CountDeMonet/ArduinoProtonPack/bargraph_rear.jpg

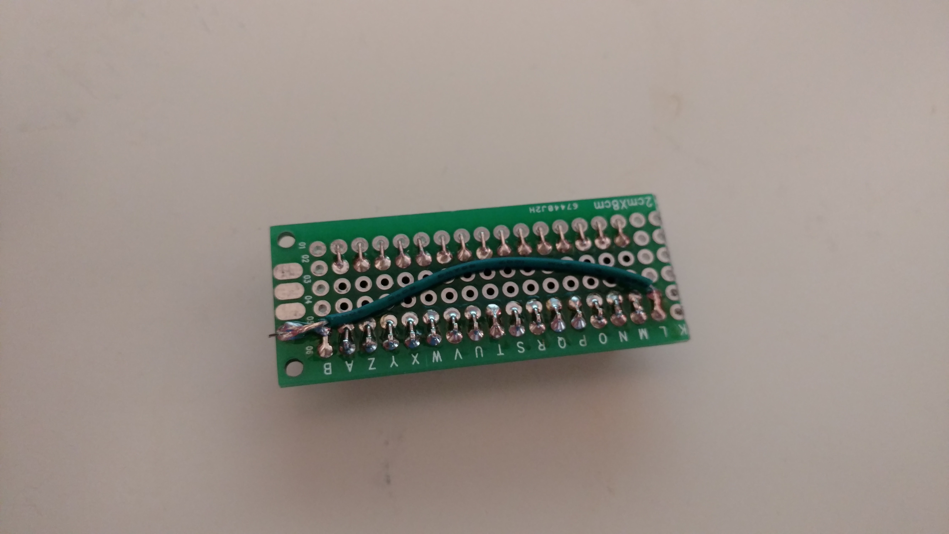
bargraph_rear.jpg
