CountDeMonet/ArduinoProtonPack/Model/83_Percent_Pack_Lefty/ion_3.stl

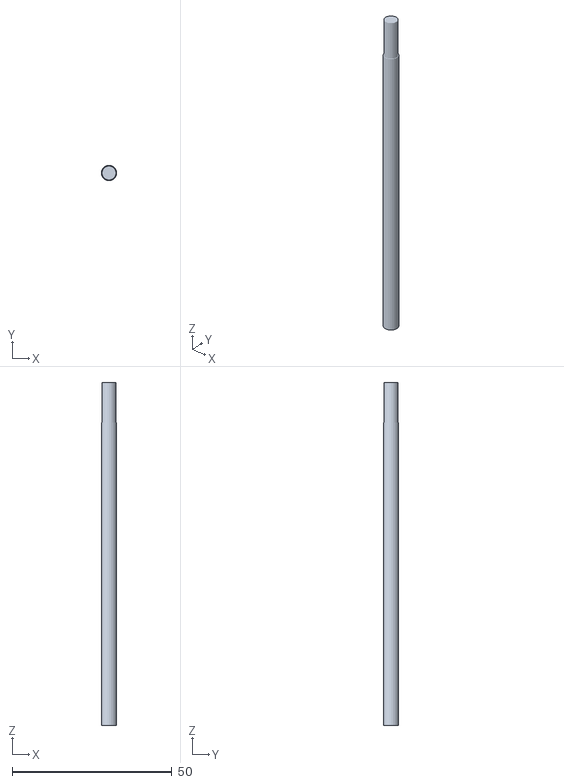
[picture p24: CAD file, 2017-09-11]
Model/83_Percent_Pack_Lefty/ion_3.stl
4.78 x 4.78 x 107.3
