CountDeMonet/ArduinoProtonPack/Model/83_Percent_Proton_Wand/front_handle_end_piece.stl

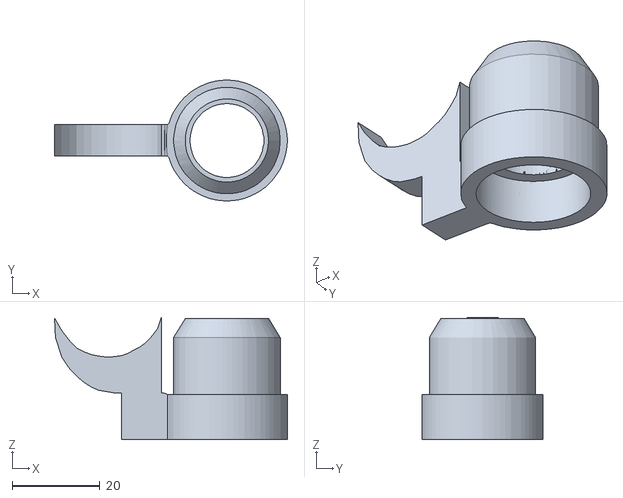
[picture p25: CAD file, 2017-10-17]
Model/83_Percent_Proton_Wand/front_handle_end_piece.stl
53.1 x 27.5 x 27.9
