CountDeMonet/ArduinoProtonPack/Model/SpiritHalloweenProtonPackMods/gunbracket_base.stl

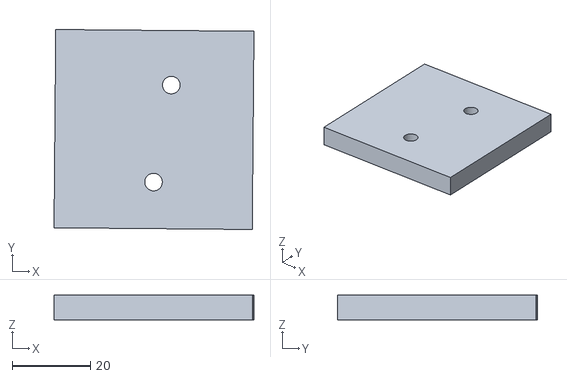
[picture p26: CAD file, 2017-10-16]
Model/SpiritHalloweenProtonPackMods/gunbracket_base.stl
51.2 x 51.2 x 6.35
