CountDeMonet/ArduinoProtonPack/Model/83_Percent_Pack/syncgen_5.stl

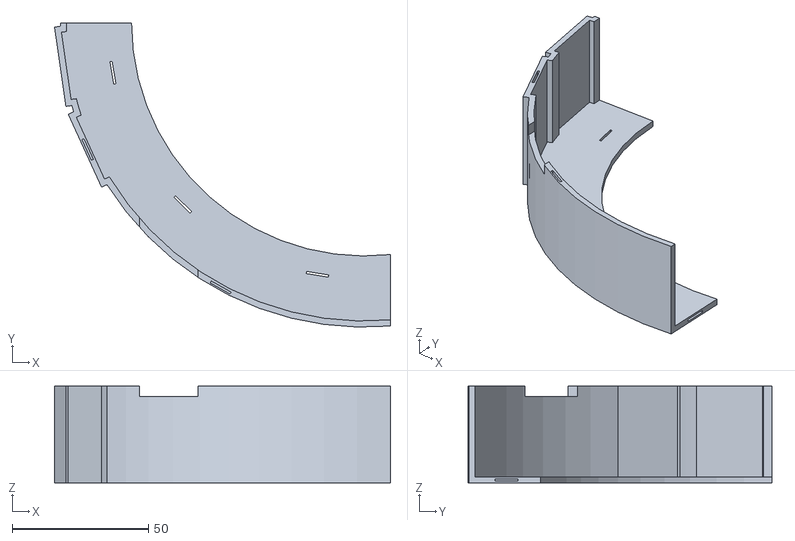
[picture p27: CAD file, 2017-10-23]
Model/83_Percent_Pack/syncgen_5.stl
123.1 x 111.4 x 35.5
