CountDeMonet/ArduinoProtonPack/Model/83_Percent_Proton_Wand/gunbox_back_panel_knob.stl

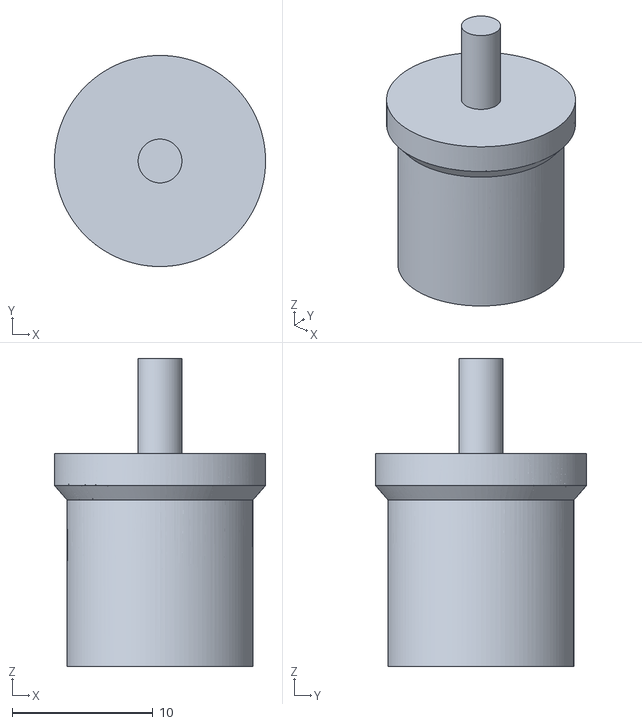
[picture p28: CAD file, 2017-10-08]
Model/83_Percent_Proton_Wand/gunbox_back_panel_knob.stl
15.0 x 15.0 x 21.9
