CountDeMonet/ArduinoProtonPack/Model/SpiritHalloweenProtonPackMods/powercell_neopixel_mount.stl

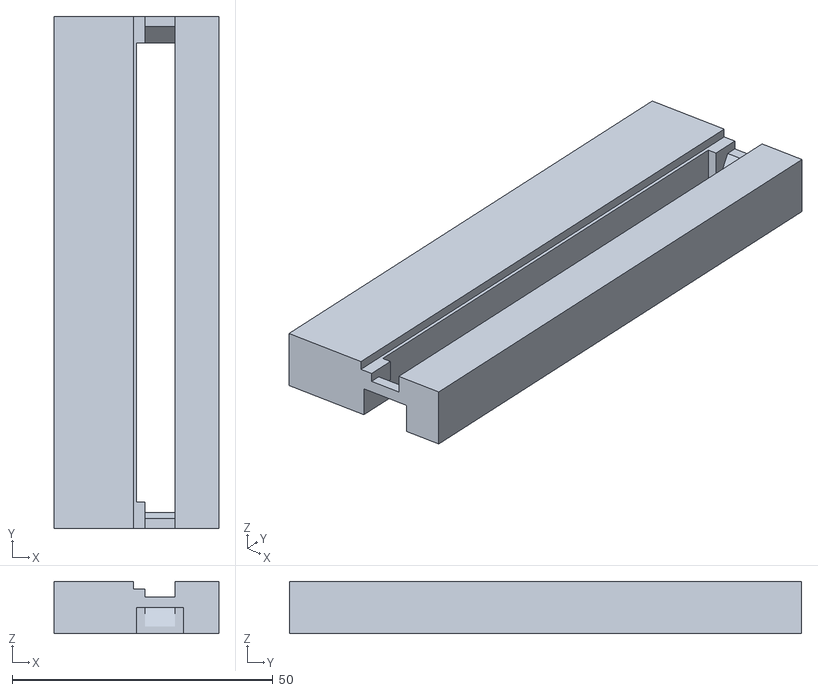
[picture p29: CAD file, 2017-10-15]
Model/SpiritHalloweenProtonPackMods/powercell_neopixel_mount.stl
31.6 x 98.2 x 10.00
