CountDeMonet/ArduinoProtonPack/Model/83_Percent_Pack/base_1.stl

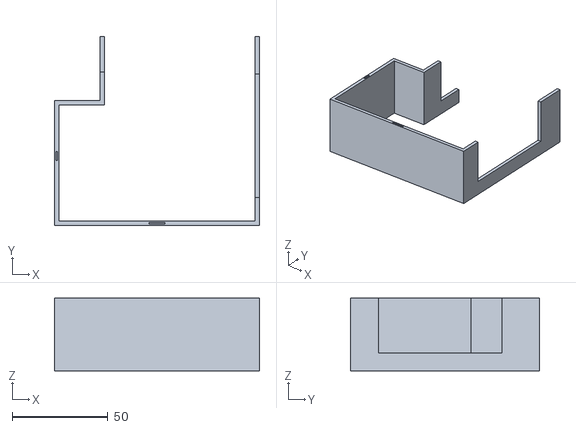
[picture p30: CAD file, 2017-10-23]
Model/83_Percent_Pack/base_1.stl
107.1 x 98.7 x 38.1
