CountDeMonet/ArduinoProtonPack/Model/83_Percent_Proton_Wand/front_green_tube_barbs.stl

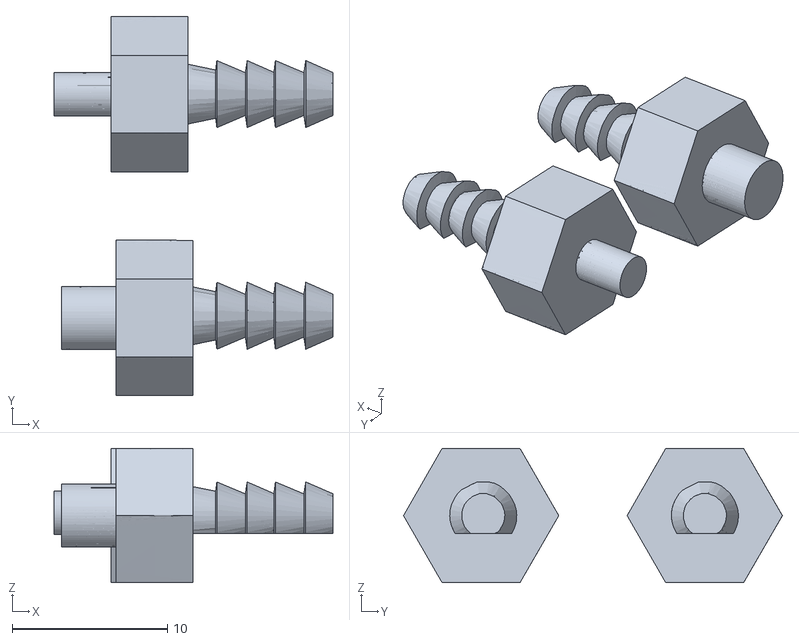
[picture p31: CAD file, 2017-10-07]
Model/83_Percent_Proton_Wand/front_green_tube_barbs.stl
17.9 x 24.4 x 8.66
