CountDeMonet/ArduinoProtonPack/Model/SpiritHalloweenProtonPackMods/cyclotron_individual_neopixel.stl

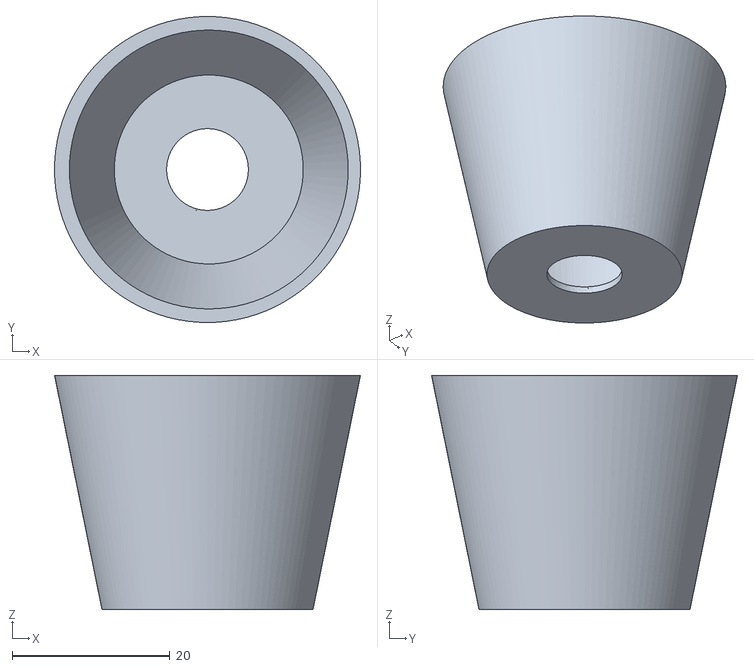
[picture p32: CAD file, 2017-10-14]
Model/SpiritHalloweenProtonPackMods/cyclotron_individual_neopixel.stl
38.8 x 38.8 x 29.7
