CountDeMonet/ArduinoProtonPack/Model/83_Percent_Pack/plating_3.stl

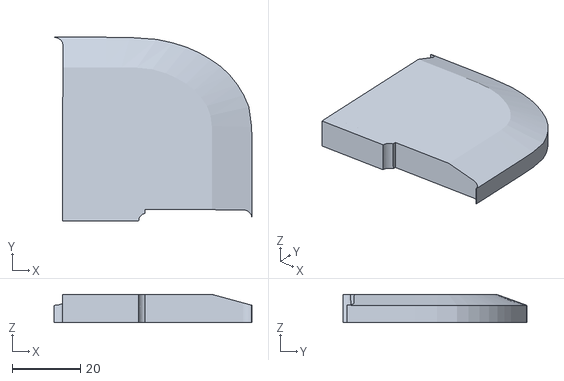
[picture p33: CAD file, 2017-10-23]
Model/83_Percent_Pack/plating_3.stl
58.1 x 53.9 x 8.30
