CountDeMonet/ArduinoProtonPack/Model/83_Percent_Proton_Wand/front_handle_hose_mount.stl

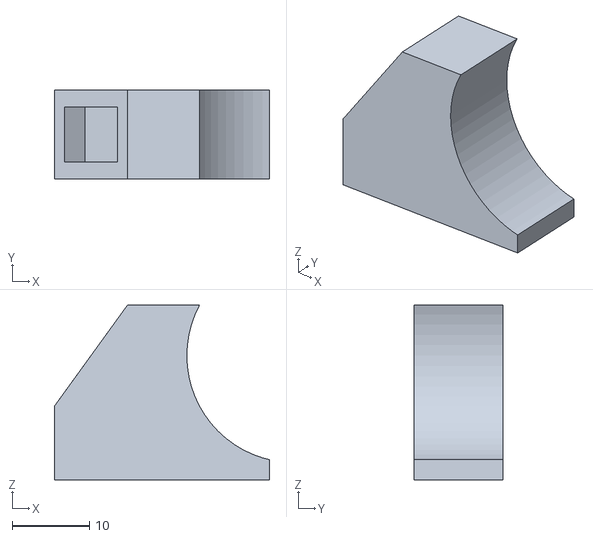
[picture p34: CAD file, 2017-09-26]
Model/83_Percent_Proton_Wand/front_handle_hose_mount.stl
27.8 x 11.4 x 22.6
