CountDeMonet/ArduinoProtonPack/Model/83_Percent_Pack/gunmount_3.stl

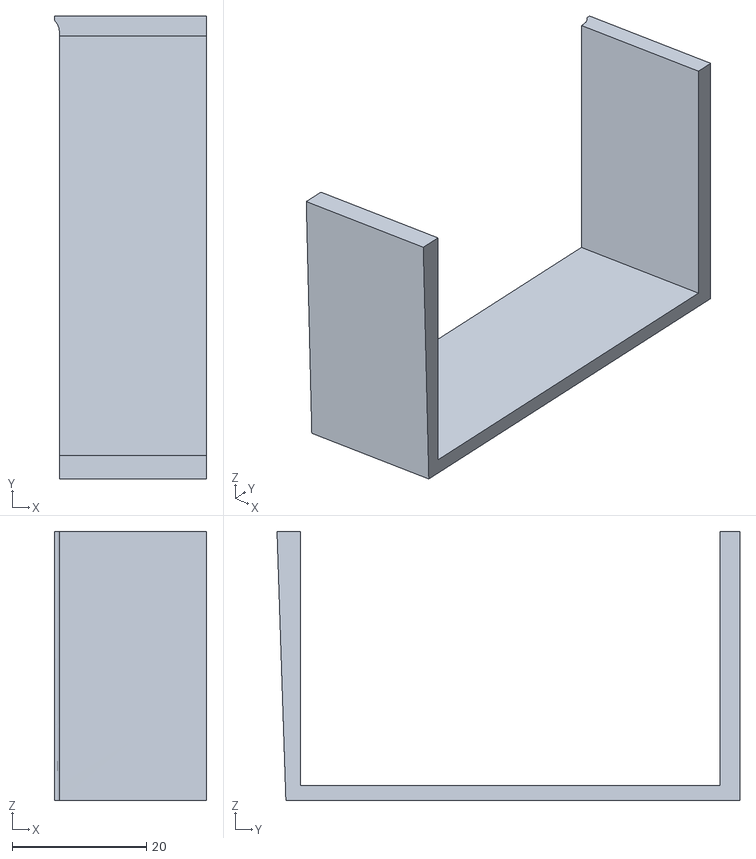
[picture p35: CAD file, 2017-10-23]
Model/83_Percent_Pack/gunmount_3.stl
22.7 x 69.0 x 40.1
