CountDeMonet/ArduinoProtonPack/Model/83_Percent_Proton_Wand/front_handle_finger_guard.stl

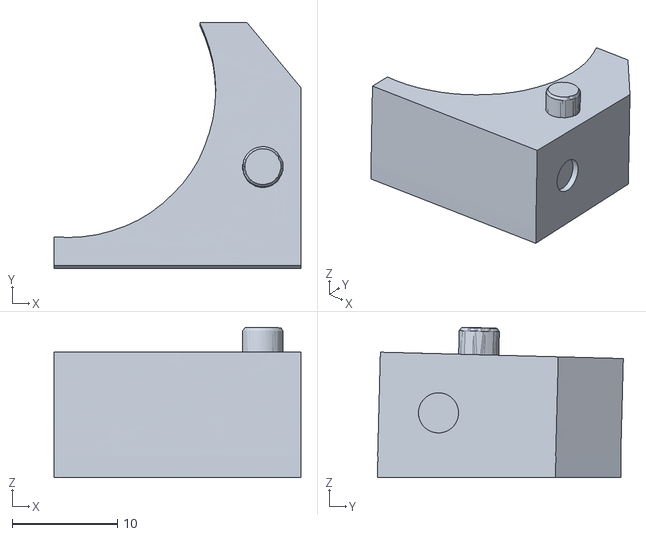
[picture p36: CAD file, 2017-09-26]
Model/83_Percent_Proton_Wand/front_handle_finger_guard.stl
23.5 x 23.4 x 14.3
