CountDeMonet/ArduinoProtonPack/Model/83_Percent_Pack/ion_1.stl

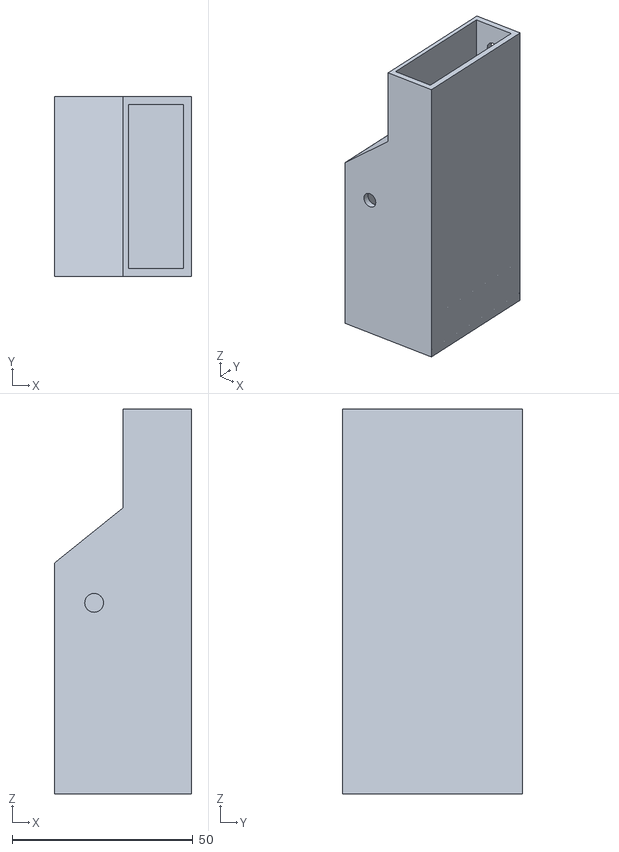
[picture p37: CAD file, 2017-10-23]
Model/83_Percent_Pack/ion_1.stl
38.0 x 49.8 x 106.6
