CountDeMonet/ArduinoProtonPack/Model/83_Percent_Proton_Wand/front_handle_wing.stl

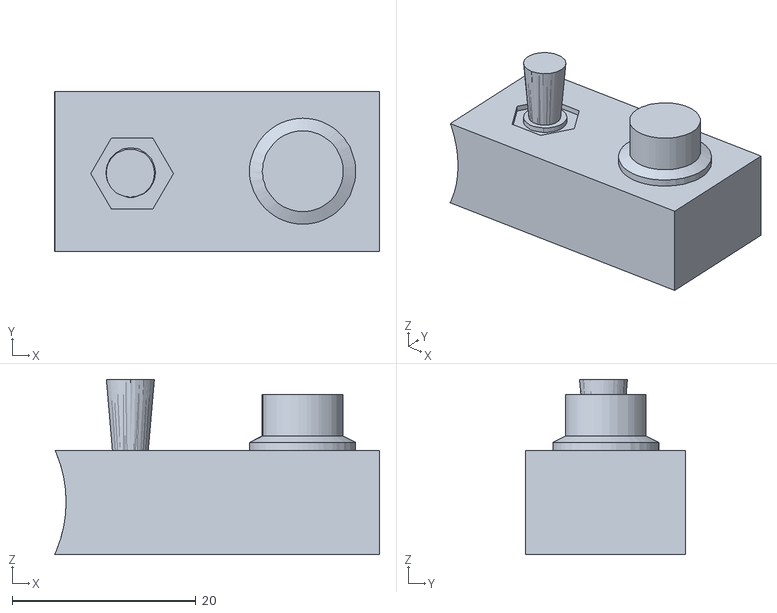
[picture p38: CAD file, 2017-09-26]
Model/83_Percent_Proton_Wand/front_handle_wing.stl
35.3 x 17.4 x 19.0
