CountDeMonet/ArduinoProtonPack/Model/83_Percent_Pack/booster_2.stl

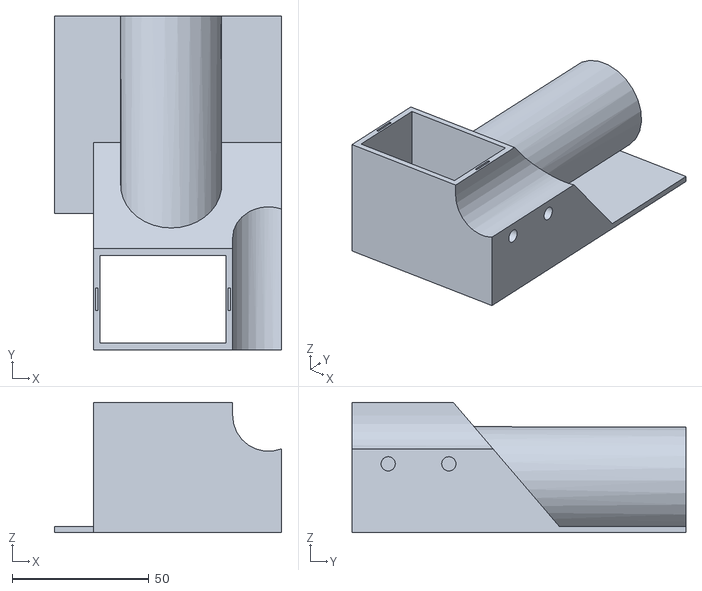
[picture p39: CAD file, 2017-10-23]
Model/83_Percent_Pack/booster_2.stl
83.0 x 122.0 x 47.6
