CountDeMonet/ArduinoProtonPack/Model/83_Percent_Proton_Wand/gunbox_back_handle_valve.stl

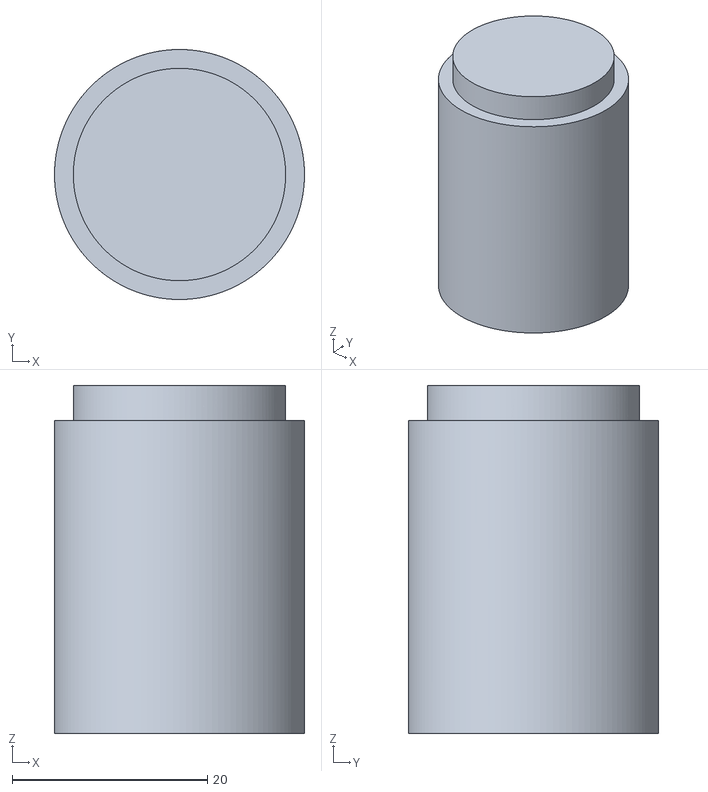
[picture p40: CAD file, 2017-09-11]
Model/83_Percent_Proton_Wand/gunbox_back_handle_valve.stl
25.6 x 25.6 x 35.6
