CountDeMonet/ArduinoProtonPack/Model/83_Percent_Proton_Wand/gunbox_side_knob.stl

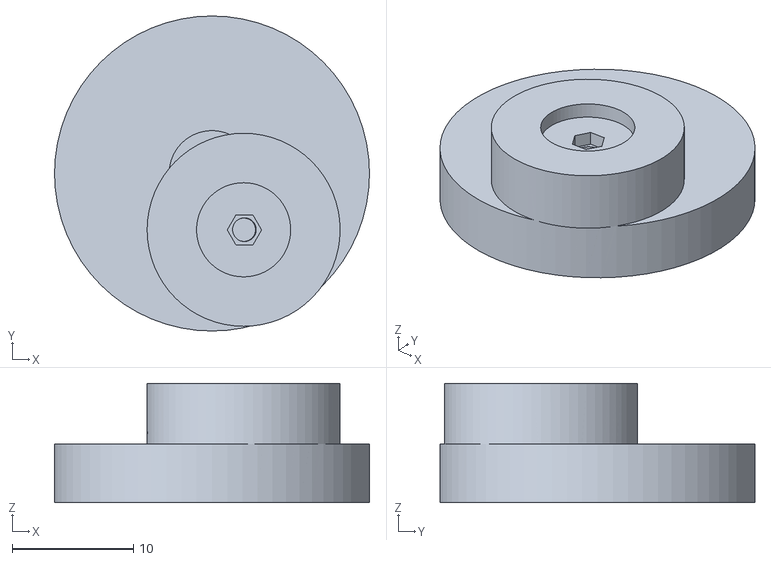
[picture p41: CAD file, 2017-09-11]
Model/83_Percent_Proton_Wand/gunbox_side_knob.stl
26.0 x 26.0 x 9.87
