CountDeMonet/ArduinoProtonPack/Model/83_Percent_Pack/crankgen_3.stl

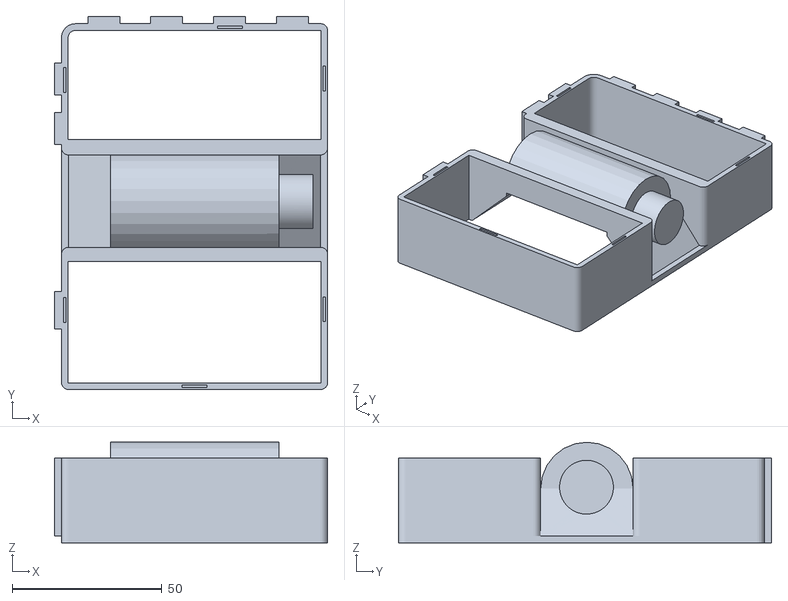
[picture p42: CAD file, 2017-10-23]
Model/83_Percent_Pack/crankgen_3.stl
91.4 x 124.6 x 33.6
