CountDeMonet/ArduinoProtonPack/Model/83_Percent_Proton_Wand/front_handle_mount.stl

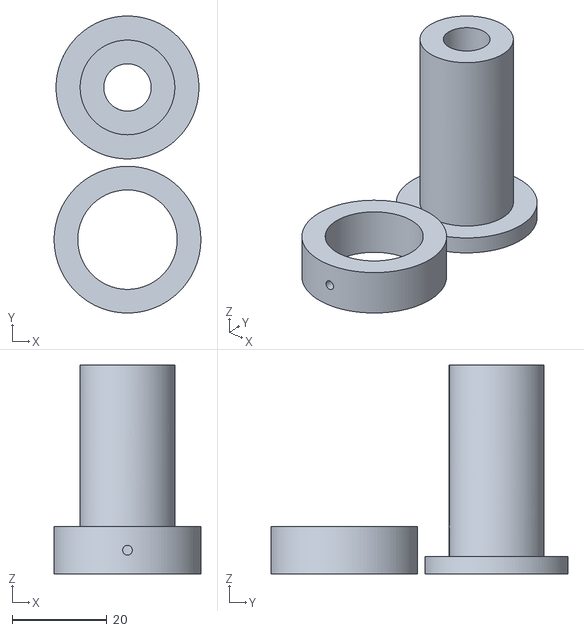
[picture p43: CAD file, 2017-09-11]
Model/83_Percent_Proton_Wand/front_handle_mount.stl
31.0 x 62.8 x 44.1
