CountDeMonet/ArduinoProtonPack/Model/83_Percent_Pack/plating_2.stl

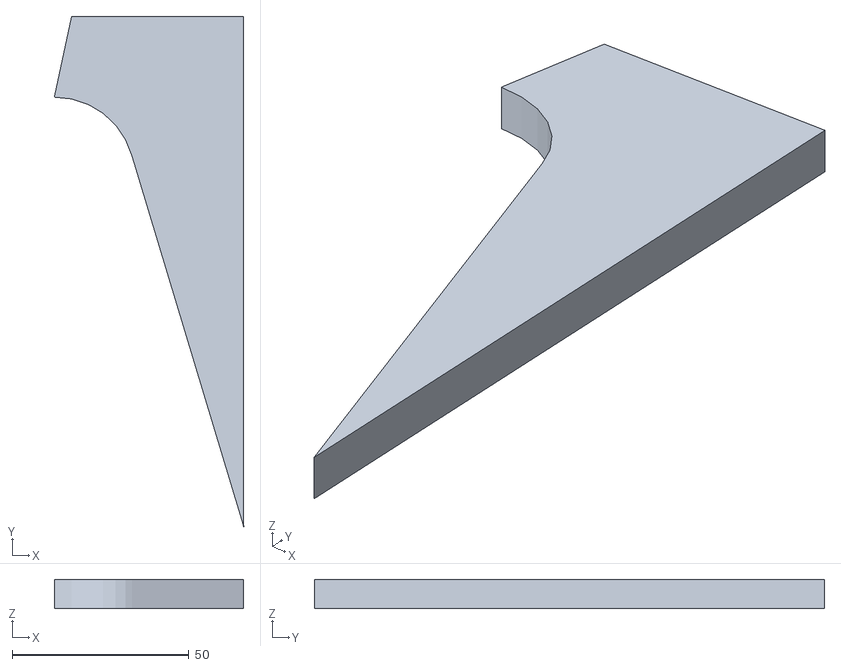
[picture p44: CAD file, 2017-10-23]
Model/83_Percent_Pack/plating_2.stl
53.5 x 144.1 x 8.31
