CountDeMonet/ArduinoProtonPack/Model/83_Percent_Proton_Wand/gunbox_grip.stl

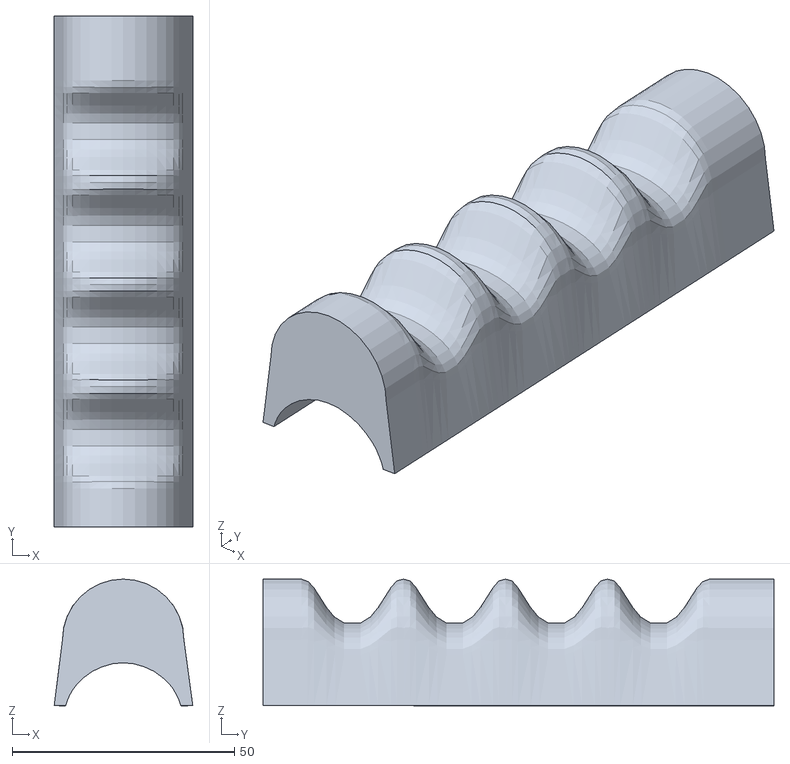
[picture p45: CAD file, 2017-09-11]
Model/83_Percent_Proton_Wand/gunbox_grip.stl
31.2 x 115.0 x 28.5
