CountDeMonet/ArduinoProtonPack/Model/83_Percent_Pack/syncgen_3.stl

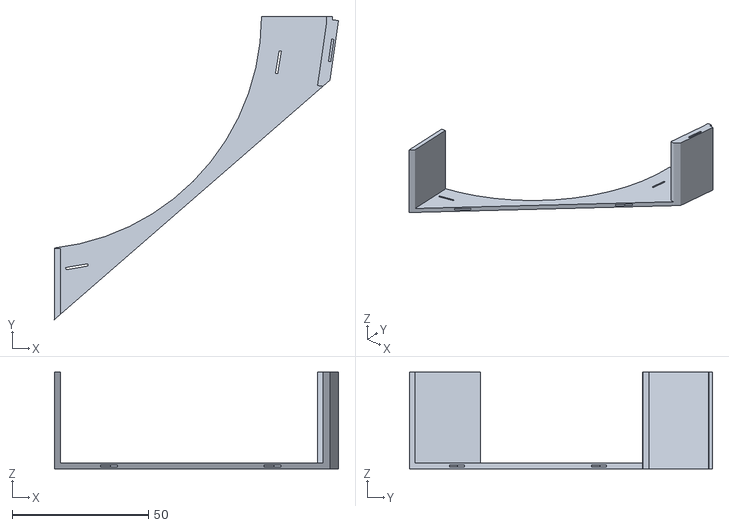
[picture p46: CAD file, 2017-10-23]
Model/83_Percent_Pack/syncgen_3.stl
104.1 x 111.1 x 35.5
