CountDeMonet/ArduinoProtonPack/Model/83_Percent_Proton_Wand/gunbox_front_cover.stl

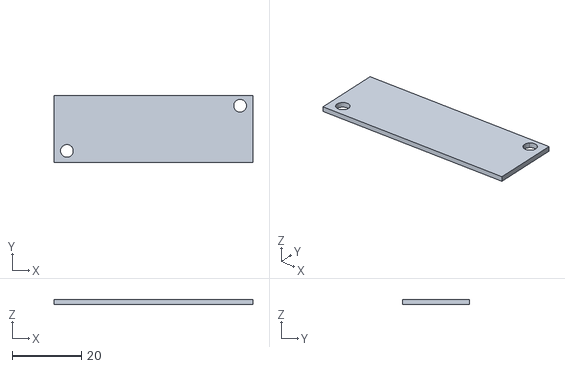
[picture p47: CAD file, 2017-09-11]
Model/83_Percent_Proton_Wand/gunbox_front_cover.stl
57.5 x 19.4 x 1.35
