CountDeMonet/ArduinoProtonPack/Model/83_Percent_Pack/crankgen_1.stl

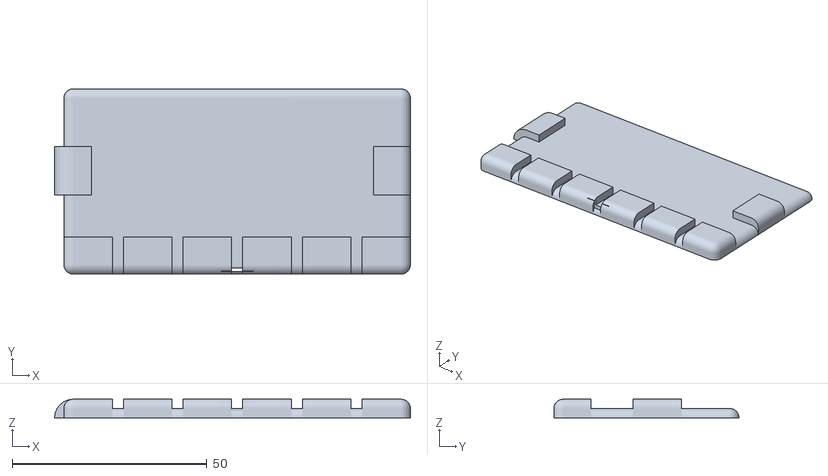
[picture p48: CAD file, 2017-10-23]
Model/83_Percent_Pack/crankgen_1.stl
91.4 x 47.5 x 4.78
