CountDeMonet/ArduinoProtonPack/Model/83_Percent_Pack/booster_3.stl

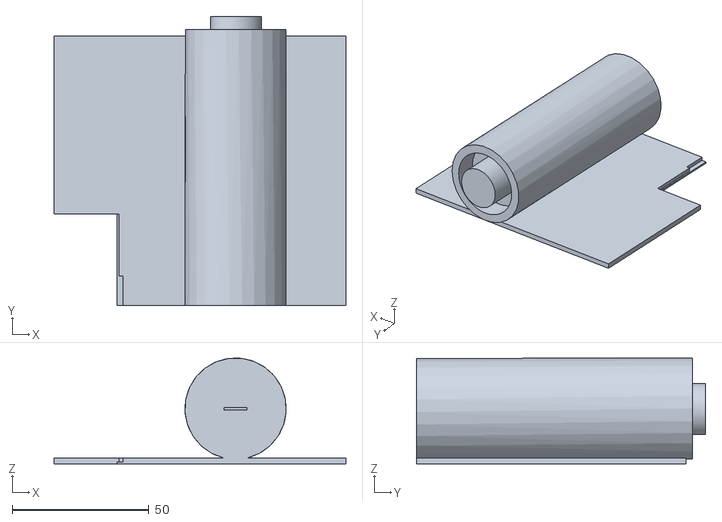
[picture p49: CAD file, 2017-10-23]
Model/83_Percent_Pack/booster_3.stl
106.7 x 105.7 x 38.7
