CountDeMonet/ArduinoProtonPack/Model/83_Percent_Proton_Wand/gunbox_base.stl

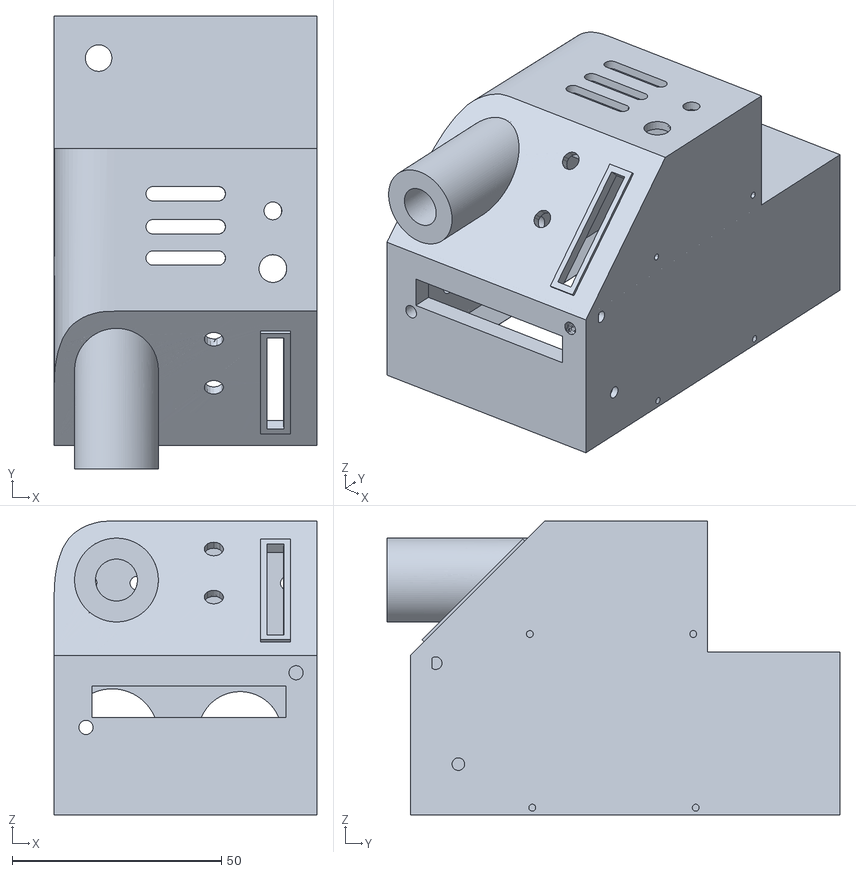
[picture p50: CAD file, 2017-09-11]
Model/83_Percent_Proton_Wand/gunbox_base.stl
62.7 x 108.2 x 70.2
