CountDeMonet/ArduinoProtonPack/Model/83_Percent_Pack/powercell_1.stl

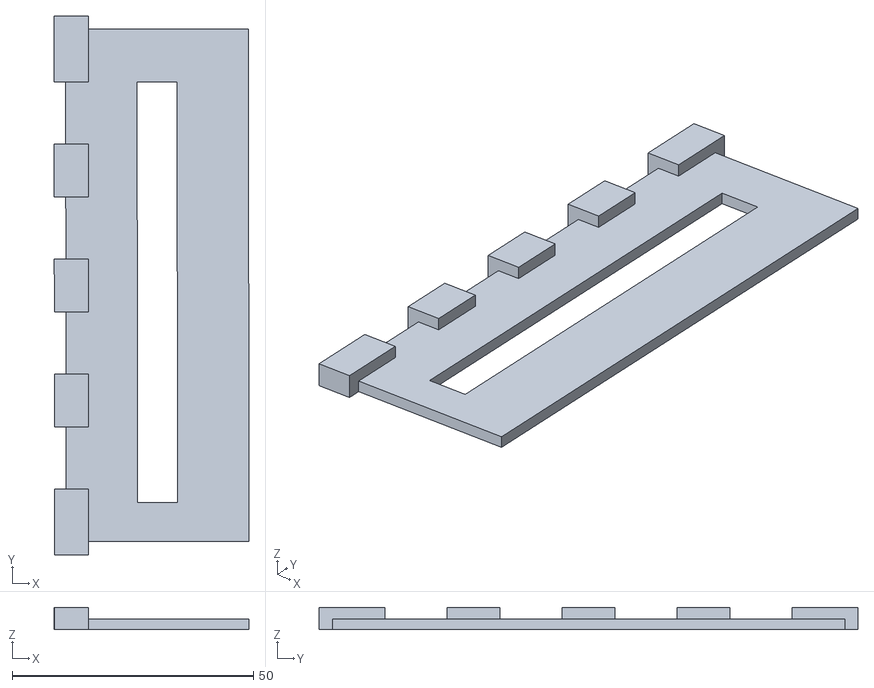
[picture p51: CAD file, 2017-10-23]
Model/83_Percent_Pack/powercell_1.stl
40.4 x 111.8 x 4.64
