CountDeMonet/ArduinoProtonPack/Model/83_Percent_Proton_Wand/gunbox_baseplate_combined.stl

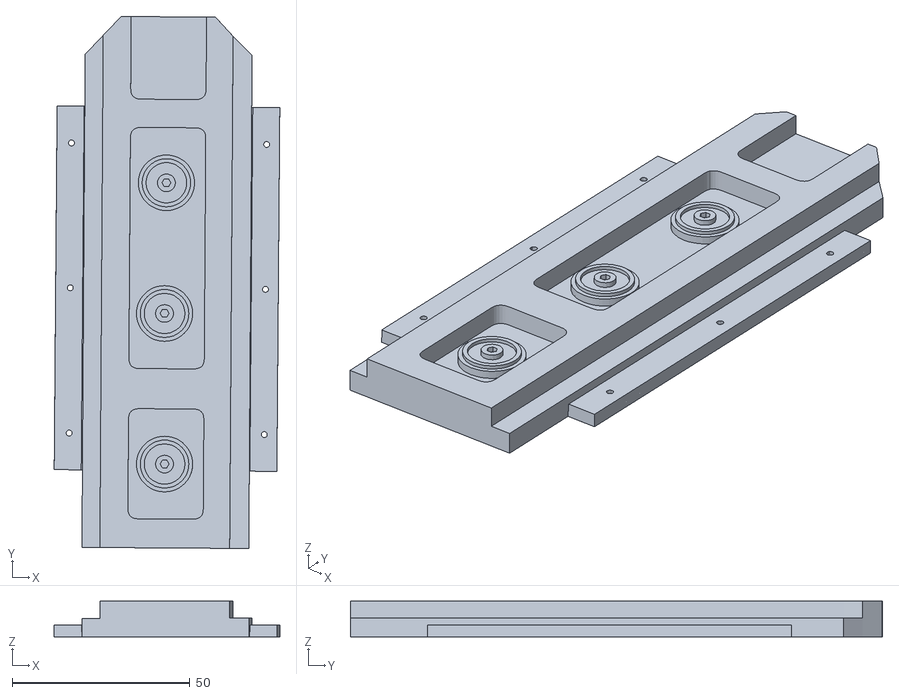
[picture p52: CAD file, 2017-09-11]
Model/83_Percent_Proton_Wand/gunbox_baseplate_combined.stl
63.5 x 149.8 x 10.1
