CountDeMonet/ArduinoProtonPack/Model/83_Percent_Pack/syncgen_4.stl

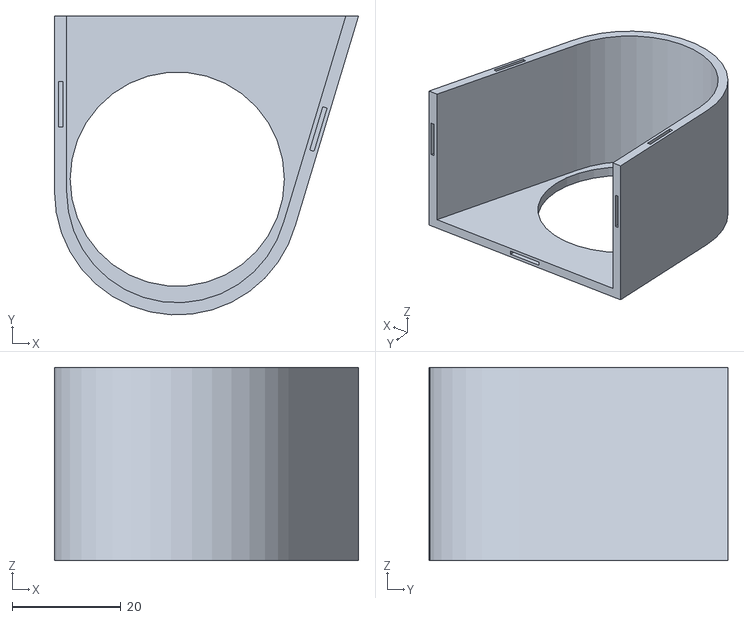
[picture p53: CAD file, 2017-10-23]
Model/83_Percent_Pack/syncgen_4.stl
55.9 x 54.9 x 35.5
