CountDeMonet/ArduinoProtonPack/Model/83_Percent_Proton_Wand/gunbox_front_trigger_box.stl

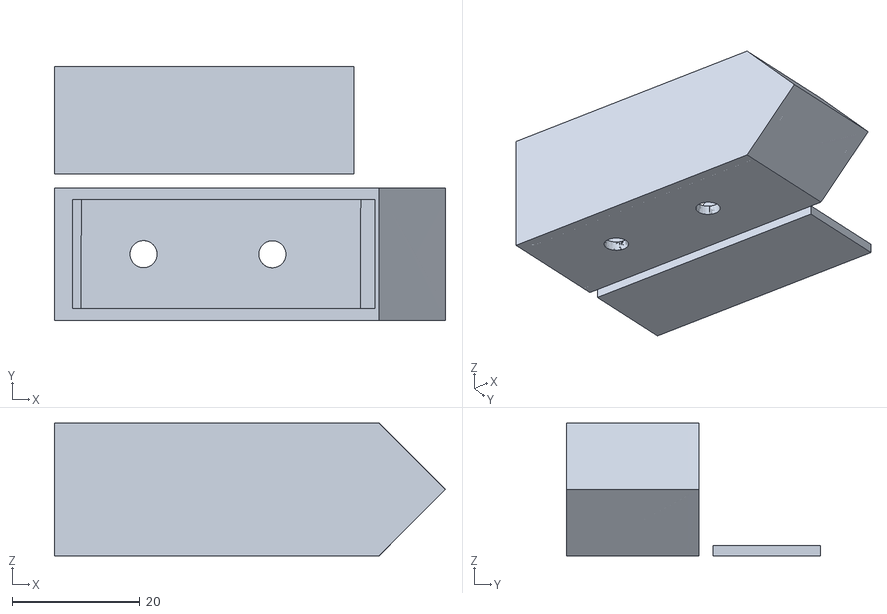
[picture p54: CAD file, 2017-09-11]
Model/83_Percent_Proton_Wand/gunbox_front_trigger_box.stl
61.2 x 39.8 x 20.8
