CountDeMonet/ArduinoProtonPack/Model/83_Percent_Pack/plating_4.stl

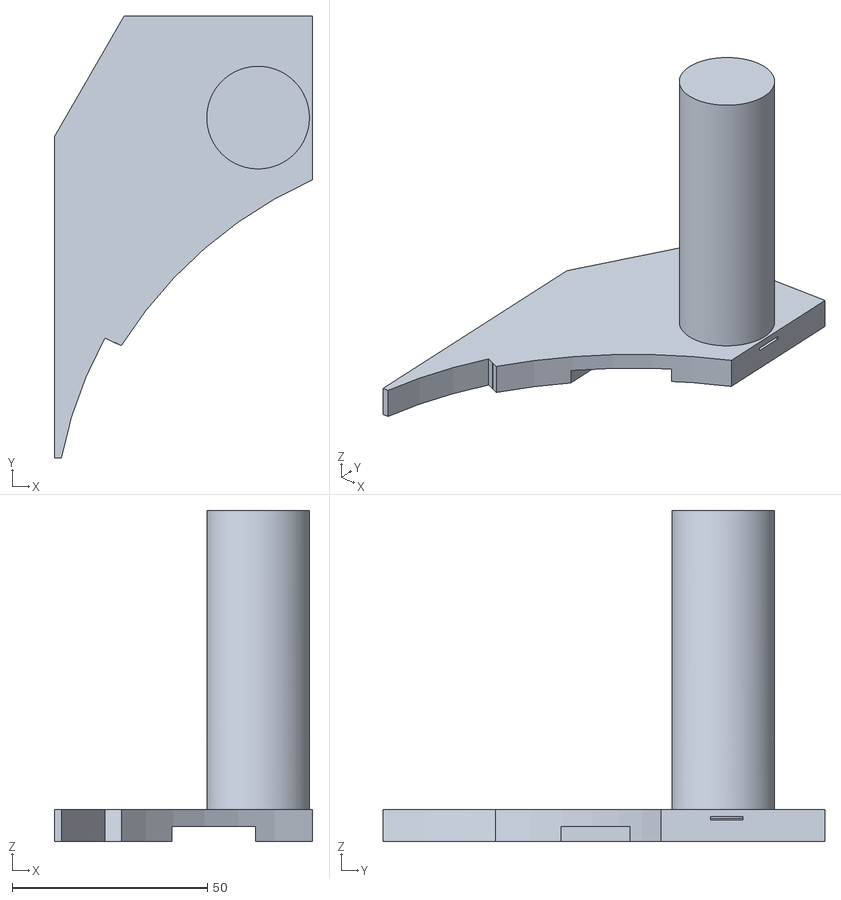
[picture p55: CAD file, 2017-10-23]
Model/83_Percent_Pack/plating_4.stl
66.2 x 113.3 x 84.9
