CountDeMonet/ArduinoProtonPack/Model/83_Percent_Proton_Wand/gunbox_front_valve.stl

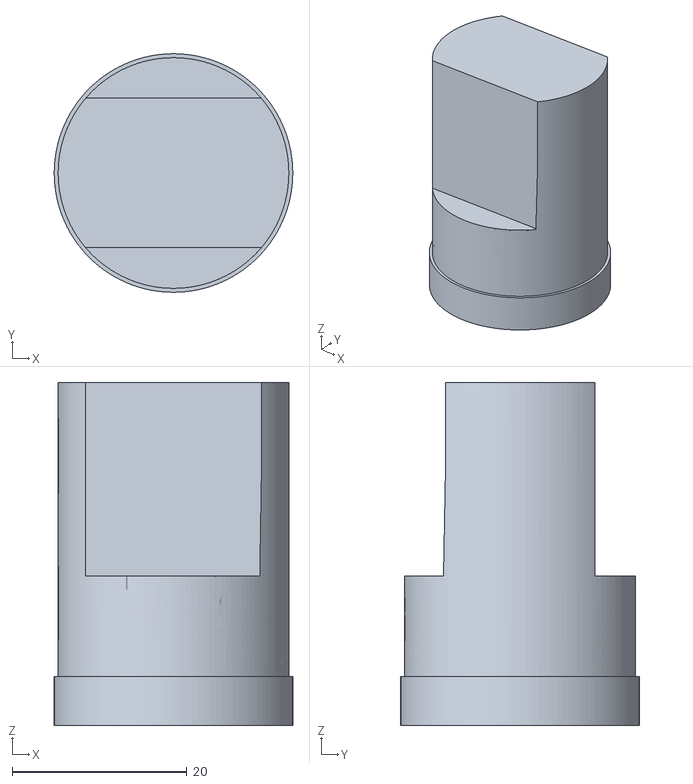
[picture p56: CAD file, 2017-09-11]
Model/83_Percent_Proton_Wand/gunbox_front_valve.stl
27.3 x 27.3 x 39.3
