CountDeMonet/ArduinoProtonPack/Model/83_Percent_Pack/syncgen_1.stl

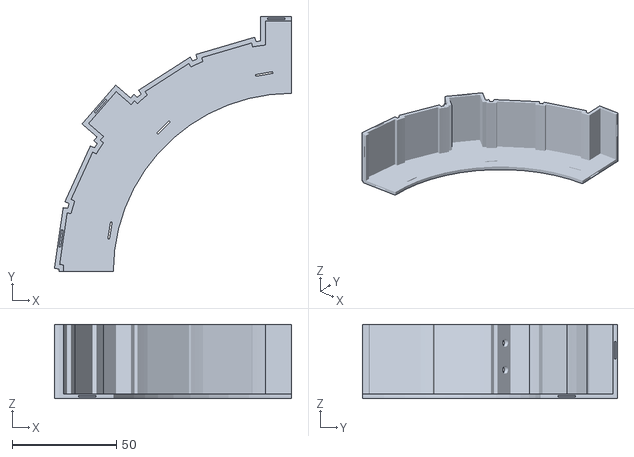
[picture p57: CAD file, 2017-10-23]
Model/83_Percent_Pack/syncgen_1.stl
113.6 x 122.2 x 35.5
