CountDeMonet/ArduinoProtonPack/Model/83_Percent_Proton_Wand/gunbox_front.stl

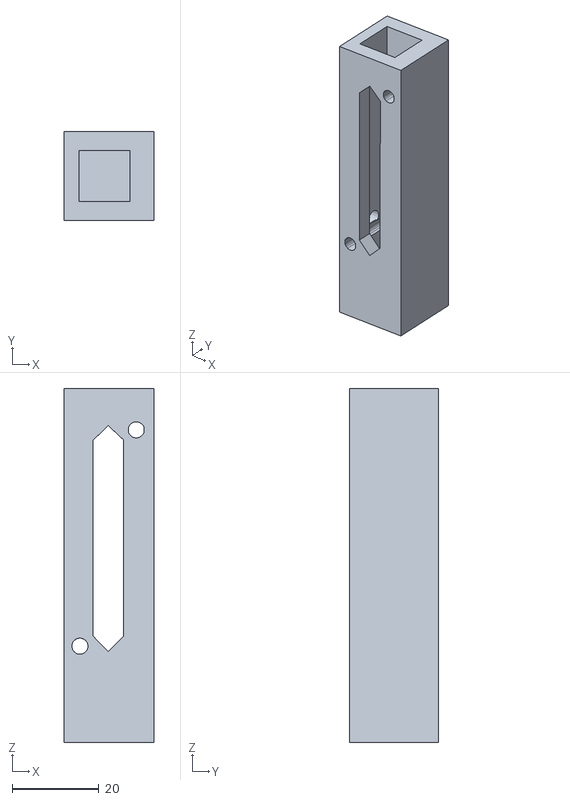
[picture p58: CAD file, 2017-09-11]
Model/83_Percent_Proton_Wand/gunbox_front.stl
20.8 x 20.7 x 81.8
