CountDeMonet/ArduinoProtonPack/Model/83_Percent_Pack/crankgen_2.stl

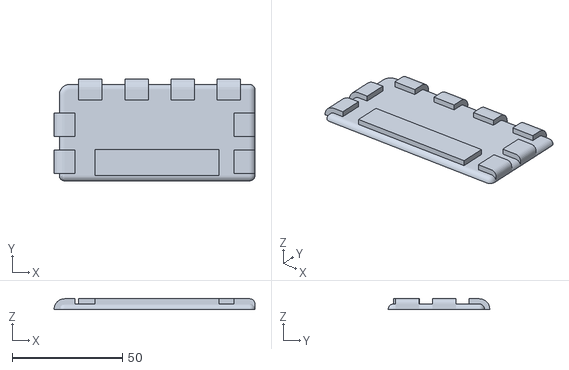
[picture p59: CAD file, 2017-10-23]
Model/83_Percent_Pack/crankgen_2.stl
91.4 x 46.2 x 4.78
