CountDeMonet/ArduinoProtonPack/Model/83_Percent_Proton_Wand/gunbox_top_knob.stl

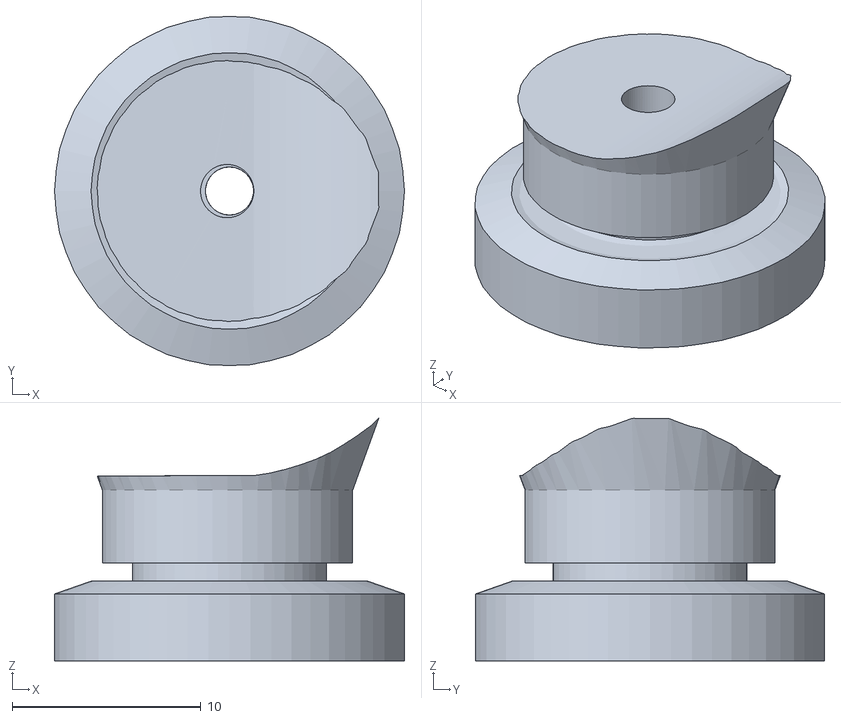
[picture p60: CAD file, 2017-09-11]
Model/83_Percent_Proton_Wand/gunbox_top_knob.stl
18.5 x 18.5 x 12.9
