CountDeMonet/ArduinoProtonPack/Model/83_Percent_Pack/base_2.stl

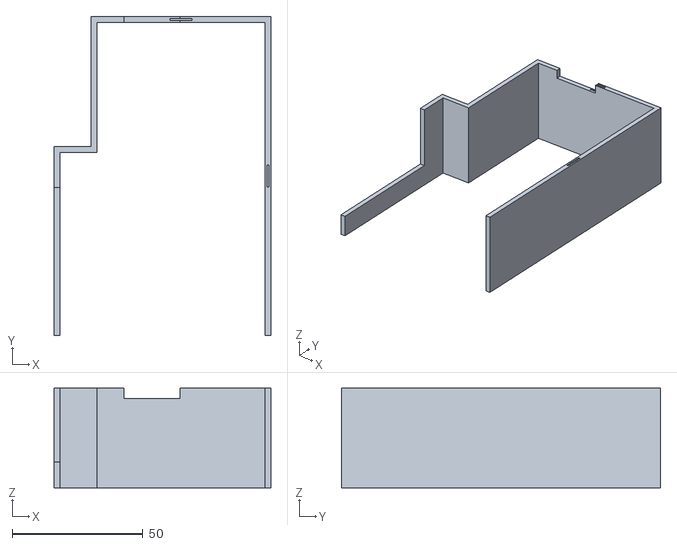
[picture p61: CAD file, 2017-10-23]
Model/83_Percent_Pack/base_2.stl
83.0 x 122.0 x 38.1
