CountDeMonet/ArduinoProtonPack/Model/83_Percent_Proton_Wand/front_nose_spacer.stl

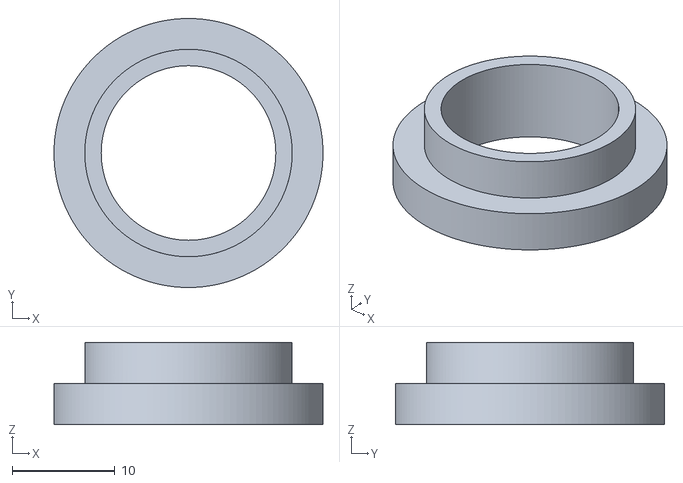
[picture p62: CAD file, 2017-09-11]
Model/83_Percent_Proton_Wand/front_nose_spacer.stl
26.2 x 26.2 x 8.00
