CountDeMonet/ArduinoProtonPack/Model/83_Percent_Proton_Wand/gunbox_heatsink.stl

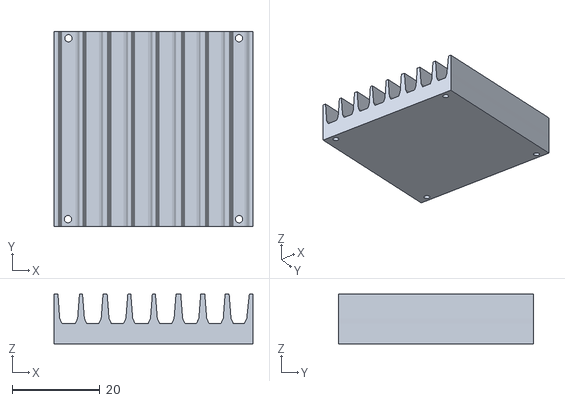
[picture p64: CAD file, 2017-09-11]
Model/83_Percent_Proton_Wand/gunbox_heatsink.stl
45.3 x 44.5 x 11.3
