CountDeMonet/ArduinoProtonPack/Model/83_Percent_Proton_Wand/clippard.stl

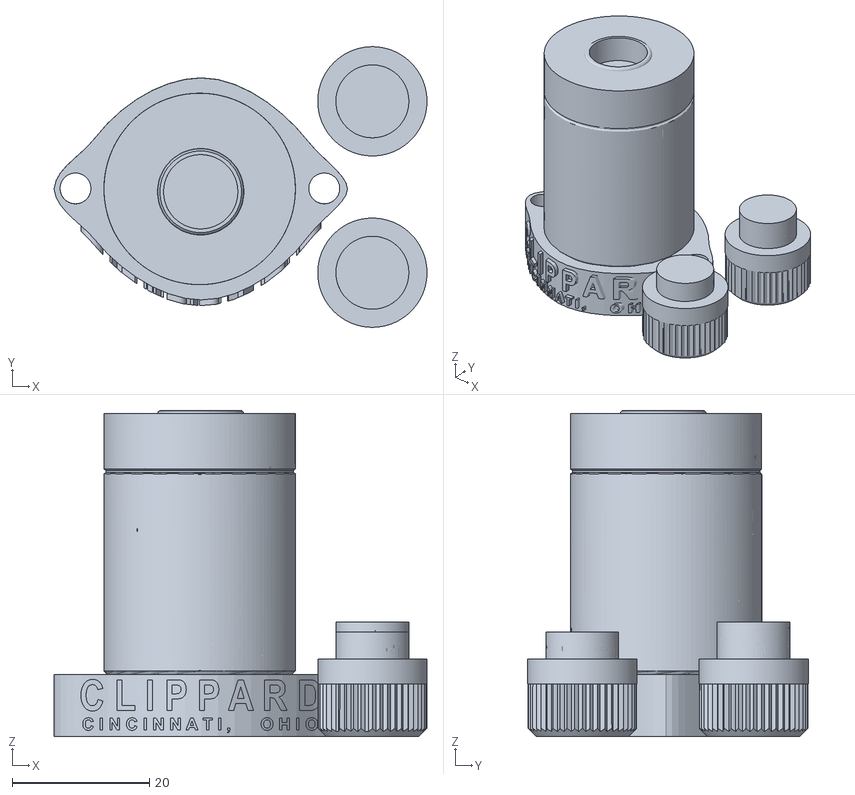
[picture p65: CAD file, 2017-09-11]
Model/83_Percent_Proton_Wand/clippard.stl
54.3 x 40.8 x 47.5
