CountDeMonet/ArduinoProtonPack/Model/83_Percent_Pack/gunmount_1.stl

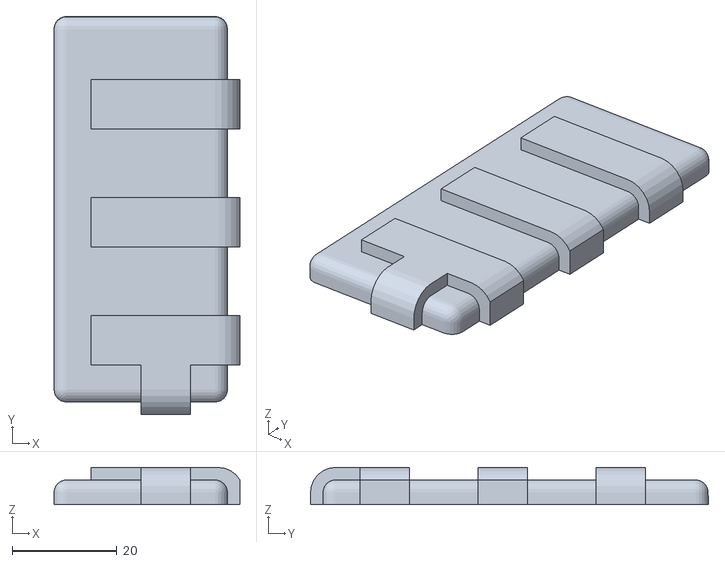
[picture p66: CAD file, 2017-10-23]
Model/83_Percent_Pack/gunmount_1.stl
35.6 x 76.1 x 7.10
