CountDeMonet/ArduinoProtonPack/Model/83_Percent_Pack/cyclotron_2.stl

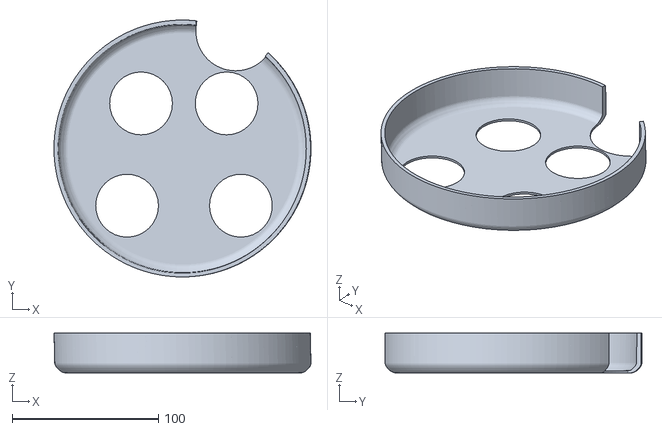
[picture p67: CAD file, 2017-10-23]
Model/83_Percent_Pack/cyclotron_2.stl
175.5 x 175.3 x 27.2
