CountDeMonet/ArduinoProtonPack/Model/83_Percent_Pack/syncgen_7.stl

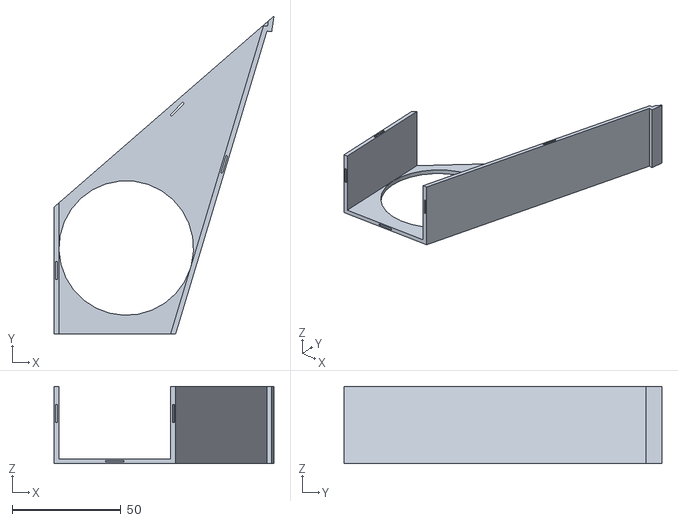
[picture p68: CAD file, 2017-10-23]
Model/83_Percent_Pack/syncgen_7.stl
101.0 x 145.9 x 35.5
