CountDeMonet/ArduinoProtonPack/Model/83_Percent_Pack/base_3.stl

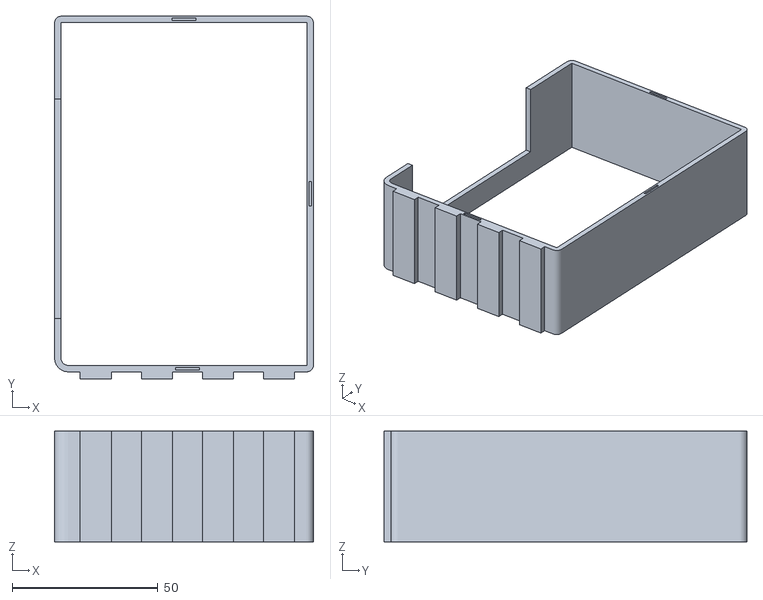
[picture p69: CAD file, 2017-10-23]
Model/83_Percent_Pack/base_3.stl
89.0 x 124.6 x 38.1
