CountDeMonet/ArduinoProtonPack/Model/83_Percent_Pack/plating_1.stl

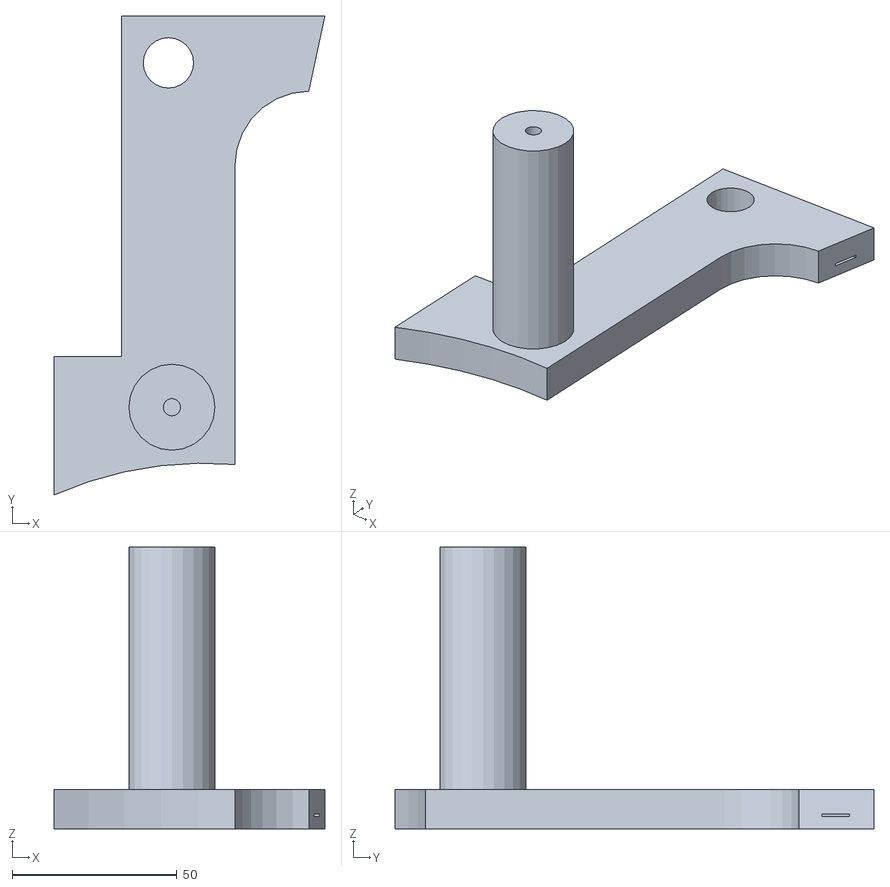
[picture p70: CAD file, 2017-10-23]
Model/83_Percent_Pack/plating_1.stl
82.1 x 145.2 x 85.4
