CountDeMonet/ArduinoProtonPack/Model/83_Percent_Pack/ion_arm_90_female.stl

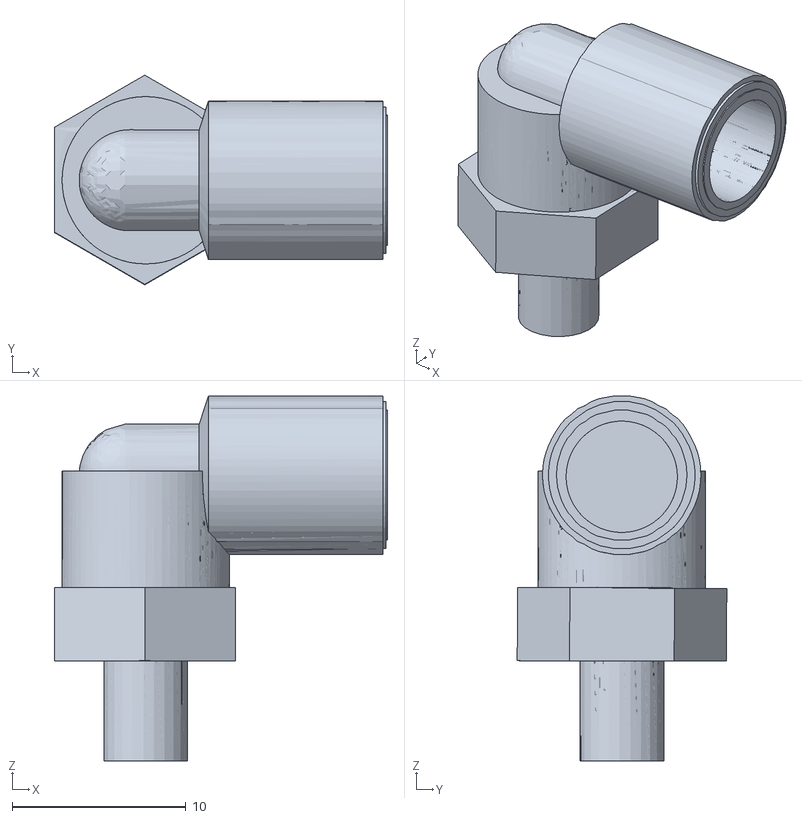
[picture p71: CAD file, 2017-10-07]
Model/83_Percent_Pack/ion_arm_90_female.stl
19.2 x 12.1 x 21.0
