CountDeMonet/ArduinoProtonPack/Model/83_Percent_Pack/booster_straight_barb.stl

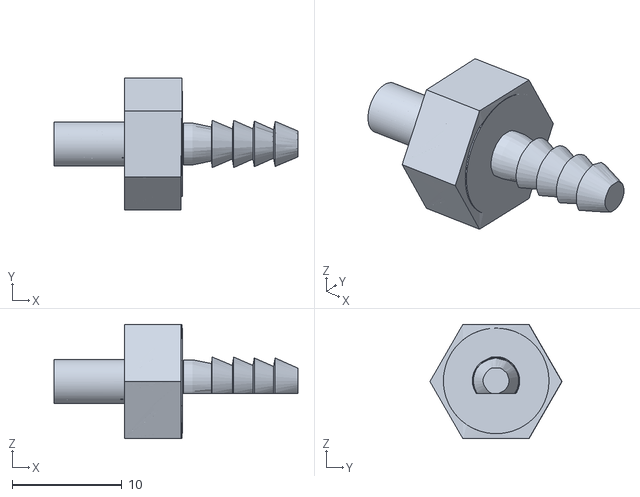
[picture p72: CAD file, 2017-10-07]
Model/83_Percent_Pack/booster_straight_barb.stl
22.3 x 12.1 x 10.4
