CountDeMonet/ArduinoProtonPack/Model/83_Percent_Pack/ribbon_cable_mount.stl

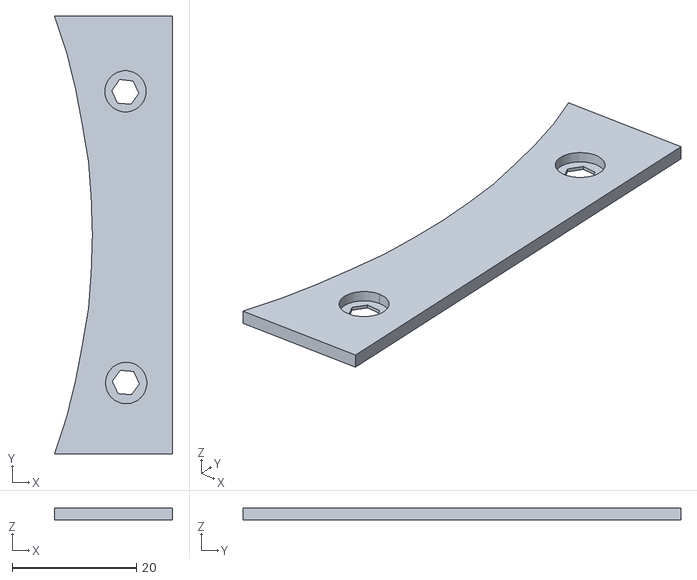
[picture p73: CAD file, 2017-10-07]
Model/83_Percent_Pack/ribbon_cable_mount.stl
19.0 x 70.5 x 1.87
