CountDeMonet/ArduinoProtonPack/Model/83_Percent_Pack/knob.stl

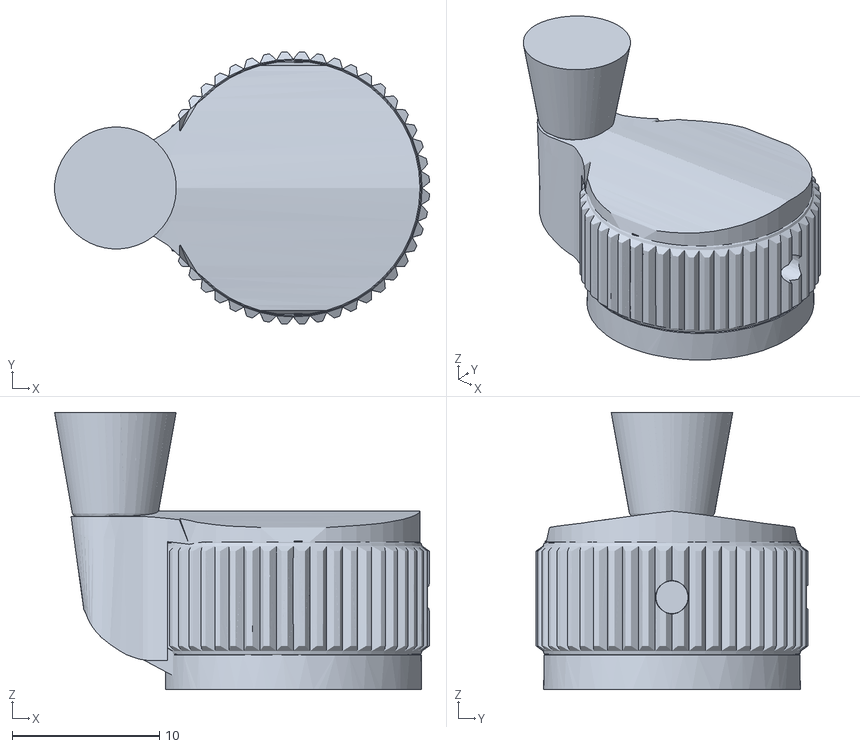
[picture p74: CAD file, 2017-10-07]
Model/83_Percent_Pack/knob.stl
25.5 x 18.5 x 18.9
