CountDeMonet/ArduinoProtonPack/Model/83_Percent_Pack/hga.stl

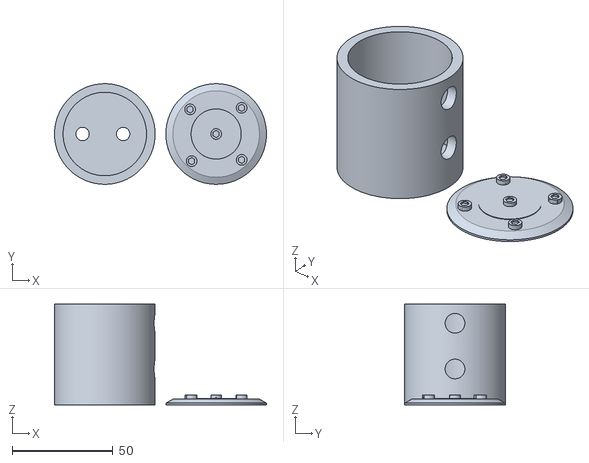
[picture p75: CAD file, 2017-10-07]
Model/83_Percent_Pack/hga.stl
105.4 x 50.1 x 50.1
