CountDeMonet/ArduinoProtonPack/Model/83_Percent_Pack/top_90_barb.stl

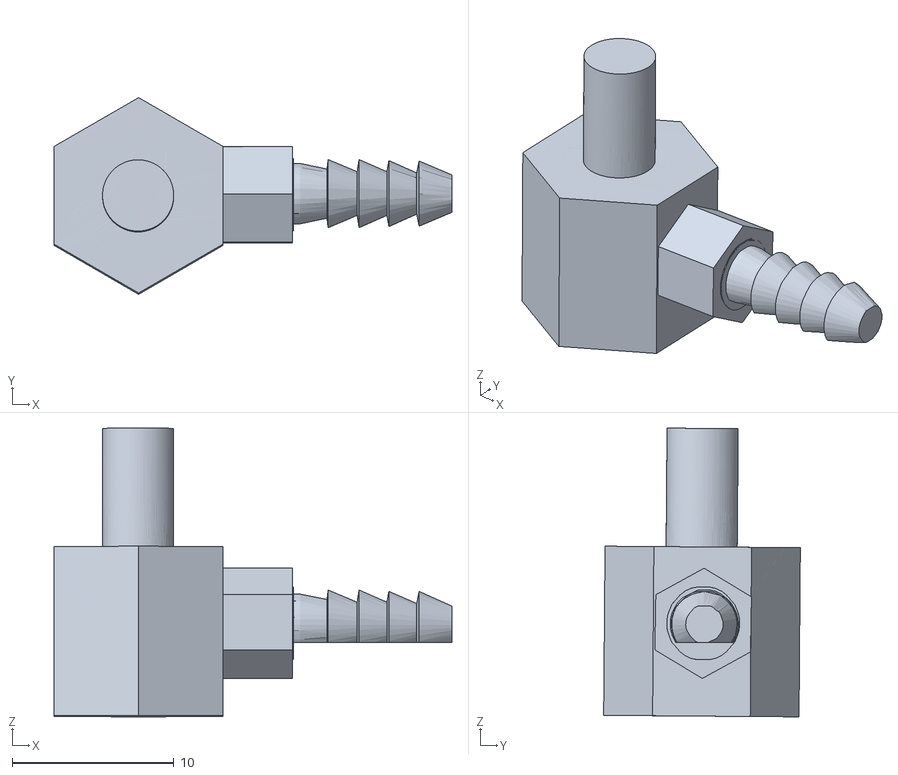
[picture p76: CAD file, 2017-10-07]
Model/83_Percent_Pack/top_90_barb.stl
24.6 x 12.2 x 17.8
