CountDeMonet/ArduinoProtonPack/Model/83_Percent_Pack/ion_rod_short.stl

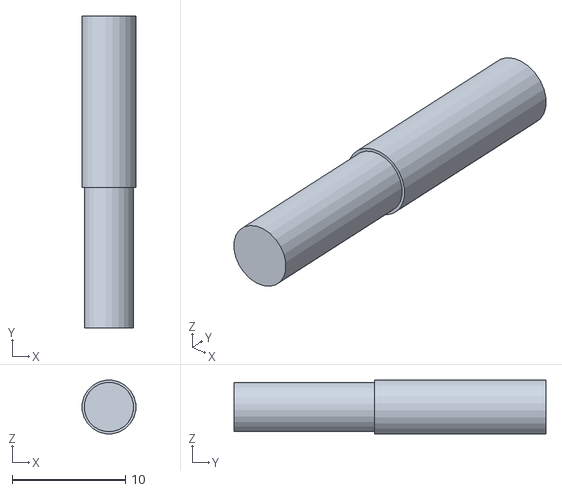
[picture p77: CAD file, 2017-10-07]
Model/83_Percent_Pack/ion_rod_short.stl
4.75 x 27.6 x 4.74
