CountDeMonet/ArduinoProtonPack/Model/83_Percent_Pack/nfilter_venting_neopixel_holder.stl

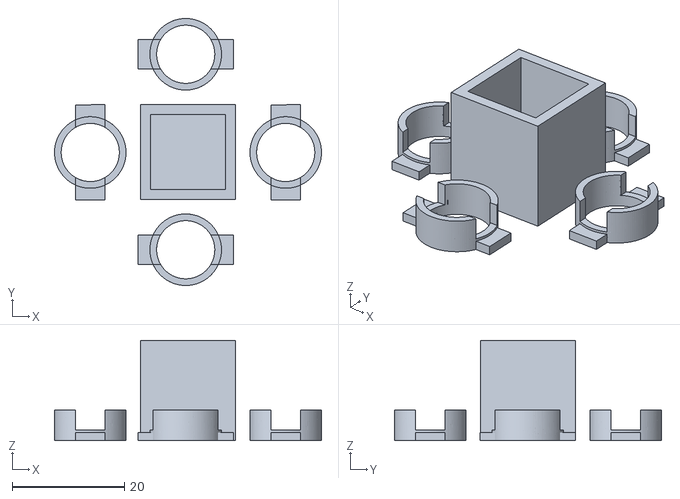
[picture p78: CAD file, 2017-09-30]
Model/83_Percent_Pack/nfilter_venting_neopixel_holder.stl
47.6 x 47.6 x 17.9
