CountDeMonet/ArduinoProtonPack/Model/83_Percent_Pack/powercell_neopixel_mount.stl

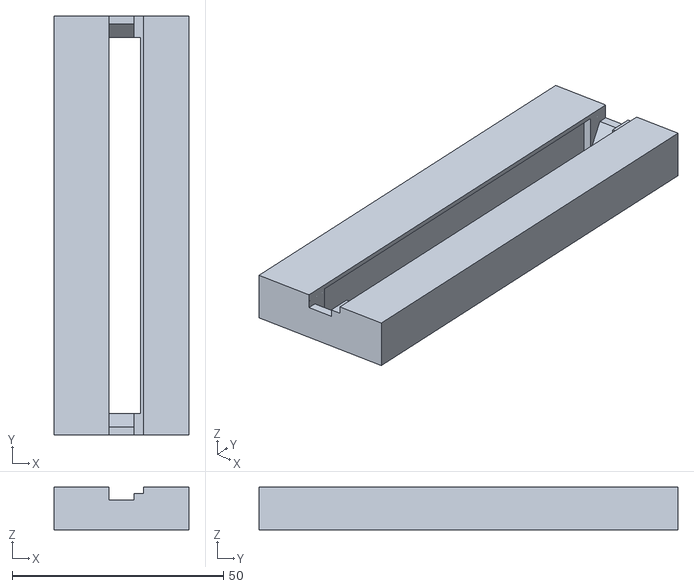
[picture p79: CAD file, 2017-09-28]
Model/83_Percent_Pack/powercell_neopixel_mount.stl
31.9 x 99.2 x 10.1
