CountDeMonet/ArduinoProtonPack/Model/83_Percent_Pack/individual_neopixel_holder.stl

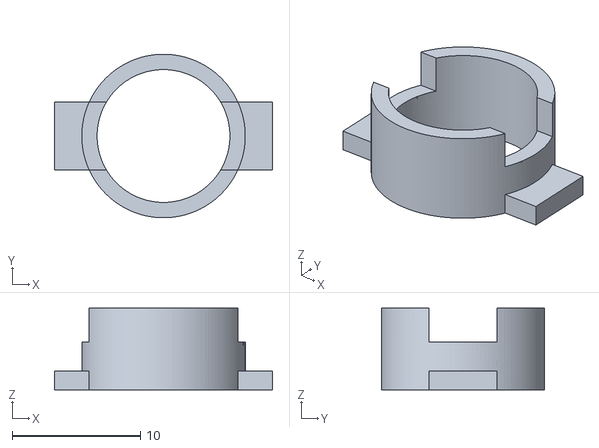
[picture p80: CAD file, 2017-09-26]
Model/83_Percent_Pack/individual_neopixel_holder.stl
17.0 x 12.7 x 6.37
