CountDeMonet/ArduinoProtonPack/Model/83_Percent_Pack/motherboard_standoff_long.stl

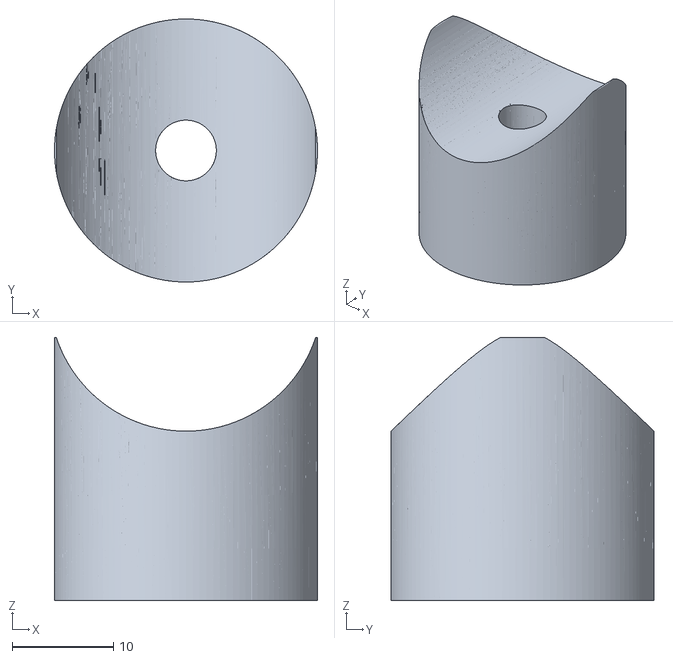
[picture p81: CAD file, 2017-09-23]
Model/83_Percent_Pack/motherboard_standoff_long.stl
26.0 x 26.0 x 26.0
