CountDeMonet/ArduinoProtonPack/Model/83_Percent_Pack/cyclotron_1_open.stl

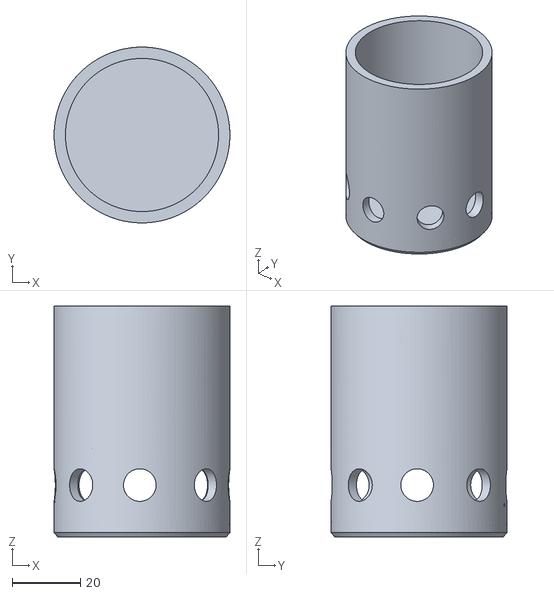
[picture p82: CAD file, 2017-09-23]
Model/83_Percent_Pack/cyclotron_1_open.stl
51.4 x 51.4 x 67.5
