CountDeMonet/ArduinoProtonPack/Model/83_Percent_Pack/syncgen_loom_mount.stl

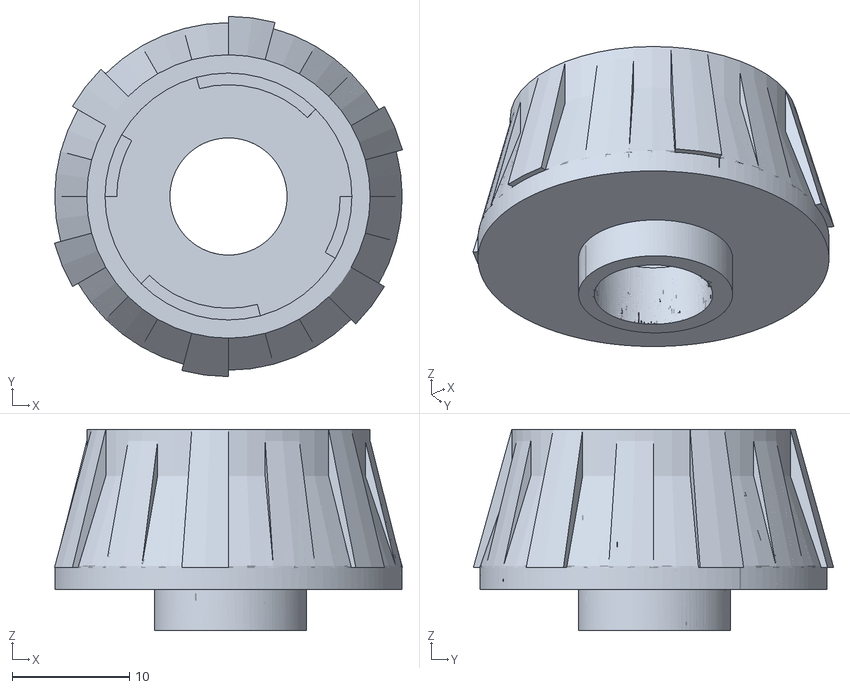
[picture p83: CAD file, 2017-09-15]
Model/83_Percent_Pack/syncgen_loom_mount.stl
29.7 x 30.8 x 17.2
