CountDeMonet/ArduinoProtonPack/Model/83_Percent_Pack/ion_2.stl

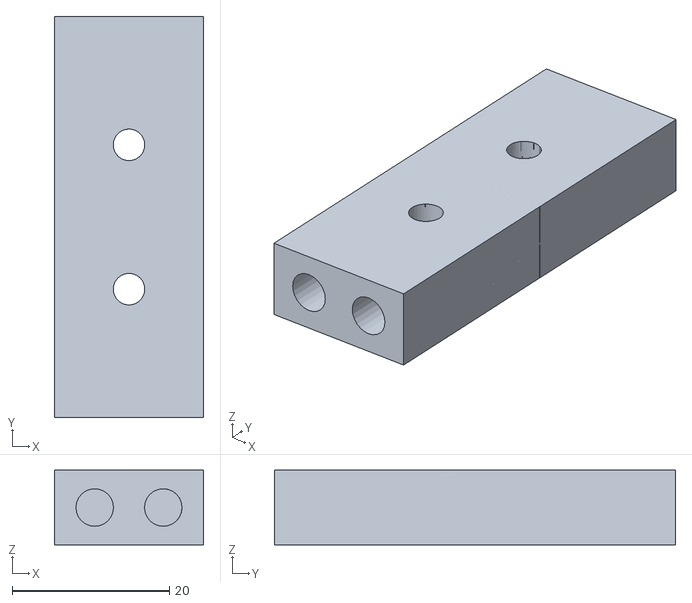
[picture p84: CAD file, 2017-09-15]
Model/83_Percent_Pack/ion_2.stl
19.0 x 51.0 x 9.49
