CountDeMonet/ArduinoProtonPack/Model/83_Percent_Pack/syncgen_6.stl

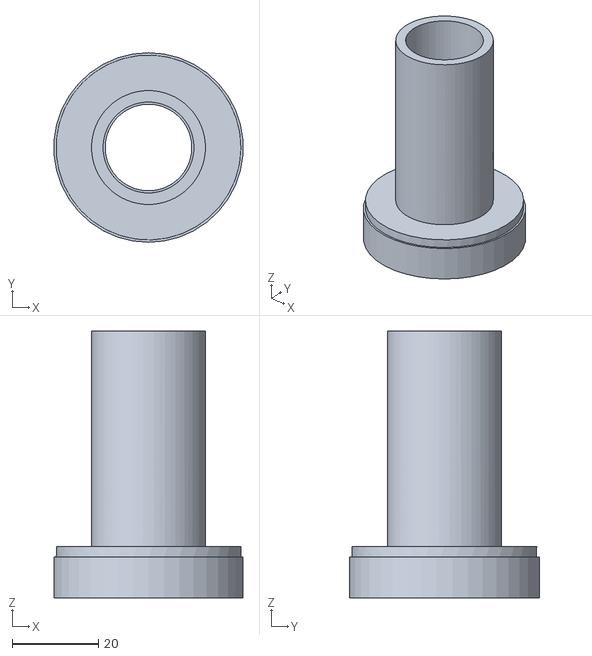
[picture p85: CAD file, 2017-09-15]
Model/83_Percent_Pack/syncgen_6.stl
43.7 x 43.8 x 61.8
