CountDeMonet/ArduinoProtonPack/Model/83_Percent_Pack/mb_mount.stl

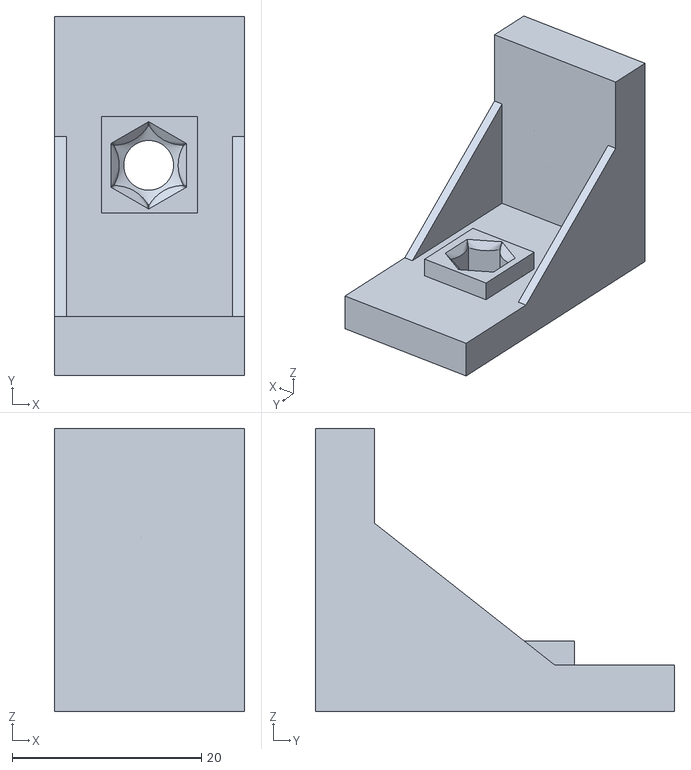
[picture p86: CAD file, 2017-09-15]
Model/83_Percent_Pack/mb_mount.stl
20.1 x 38.0 x 29.9
