CountDeMonet/ArduinoProtonPack/Model/83_Percent_Pack/connectors.stl

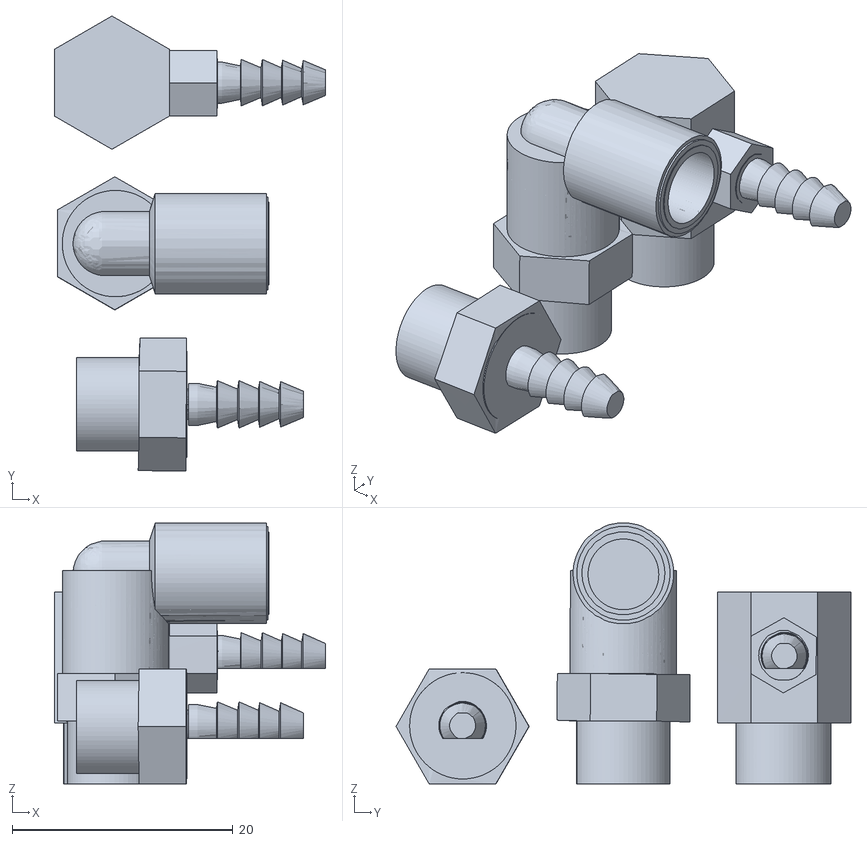
[picture p87: CAD file, 2017-09-11]
Model/83_Percent_Pack/connectors.stl
24.6 x 41.2 x 23.6
