CountDeMonet/ArduinoProtonPack/Model/83_Percent_Pack/bumper_1.stl

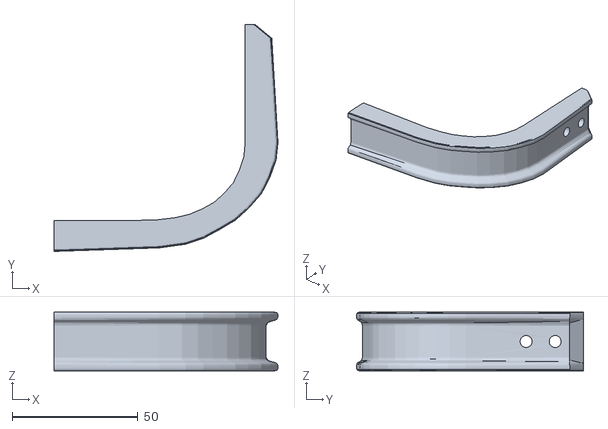
[picture p88: CAD file, 2017-09-11]
Model/83_Percent_Pack/bumper_1.stl
88.9 x 90.0 x 23.3
