CountDeMonet/ArduinoProtonPack/Model/83_Percent_Pack/bumper_4.stl

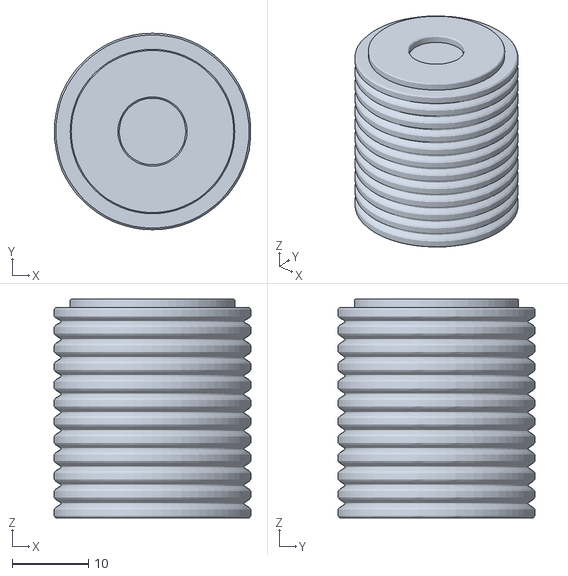
[picture p89: CAD file, 2017-09-11]
Model/83_Percent_Pack/bumper_4.stl
25.8 x 25.8 x 28.8
