CountDeMonet/ArduinoProtonPack/Model/83_Percent_Pack/booster_1.stl

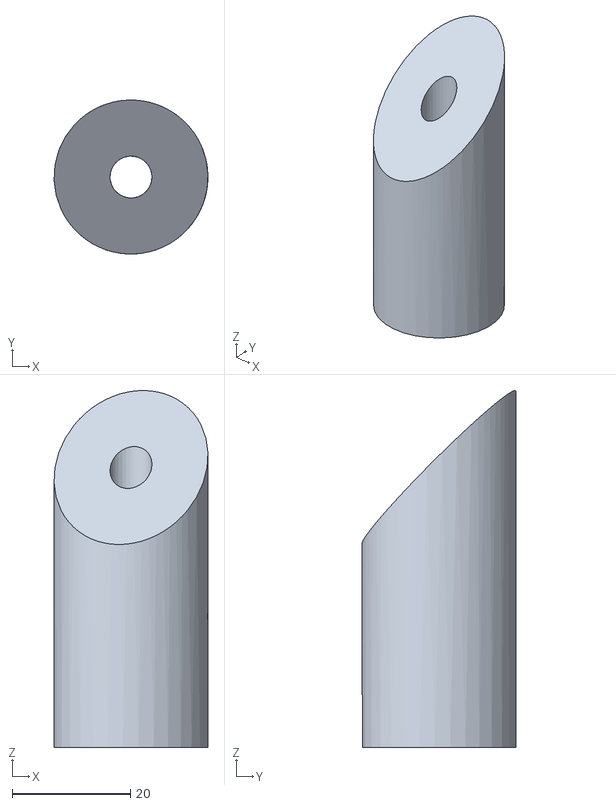
[picture p90: CAD file, 2017-09-11]
Model/83_Percent_Pack/booster_1.stl
26.1 x 26.1 x 60.4
