CountDeMonet/ArduinoProtonPack/Model/83_Percent_Pack/cyclotron_light_covers.stl

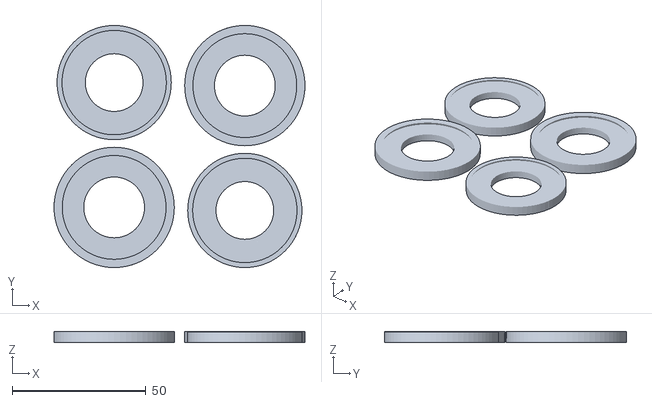
[picture p91: CAD file, 2017-09-11]
Model/83_Percent_Pack/cyclotron_light_covers.stl
93.8 x 90.5 x 4.28
