CountDeMonet/ArduinoProtonPack/Model/83_Percent_Pack/ladder.stl

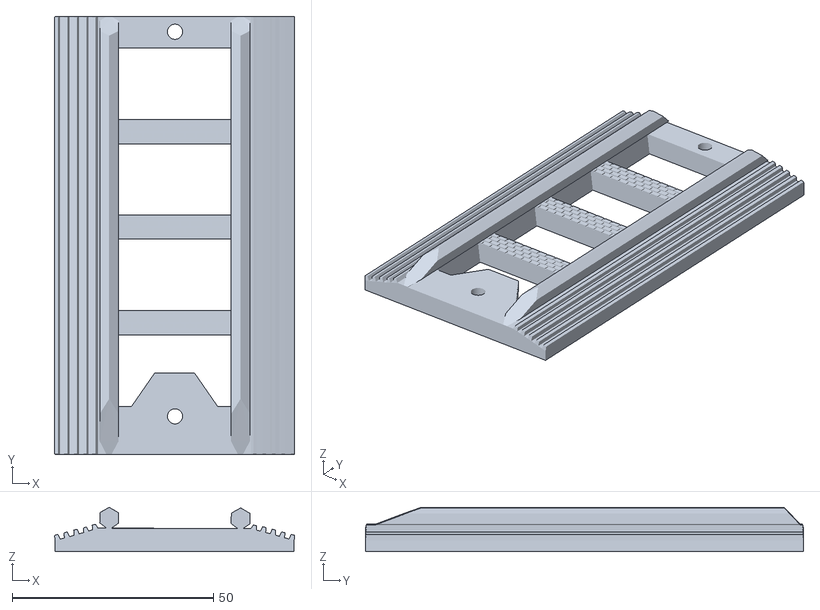
[picture p92: CAD file, 2017-09-11]
Model/83_Percent_Pack/ladder.stl
59.6 x 108.8 x 11.0
