CountDeMonet/ArduinoProtonPack/Model/83_Percent_Pack/gunbracket_2.stl

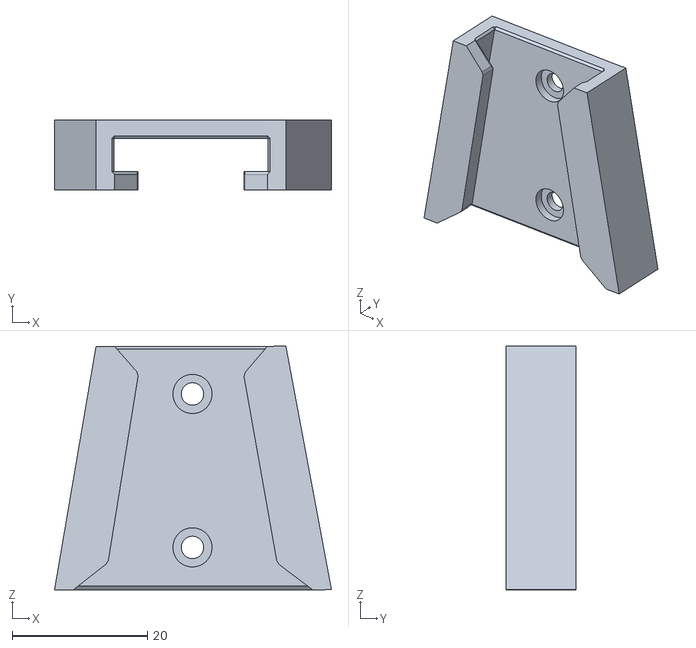
[picture p93: CAD file, 2017-09-11]
Model/83_Percent_Pack/gunbracket_2.stl
41.0 x 10.4 x 36.1
