CountDeMonet/ArduinoProtonPack/Model/83_Percent_Pack/bumper_2.stl

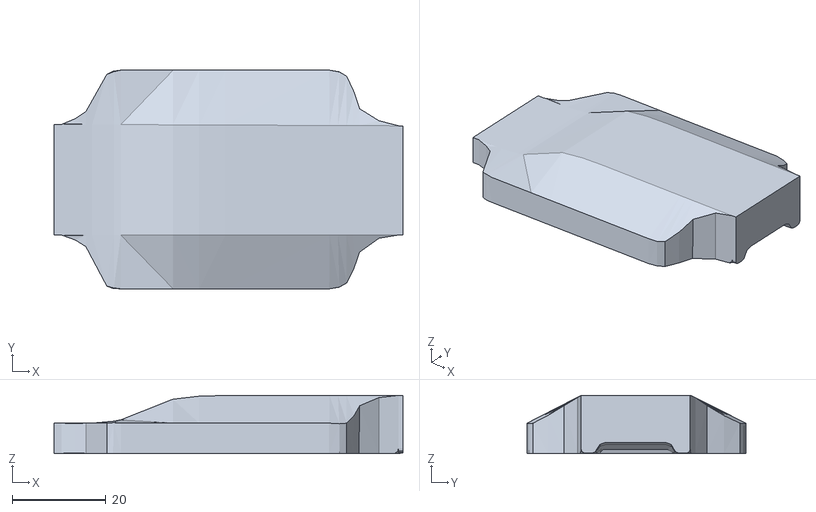
[picture p94: CAD file, 2017-09-11]
Model/83_Percent_Pack/bumper_2.stl
74.3 x 46.6 x 12.4
