CountDeMonet/ArduinoProtonPack/Model/83_Percent_Pack/clippard_base.stl

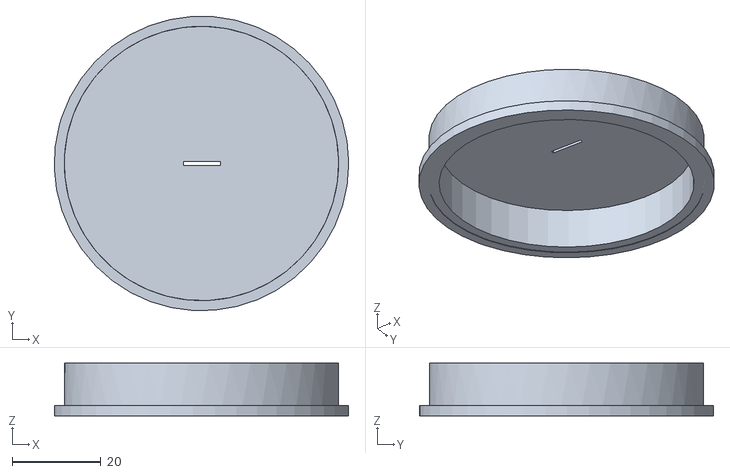
[picture p95: CAD file, 2017-09-11]
Model/83_Percent_Pack/clippard_base.stl
66.2 x 66.1 x 11.9
