CountDeMonet/ArduinoProtonPack/Model/83_Percent_Pack/cyclotron_1_closed.stl

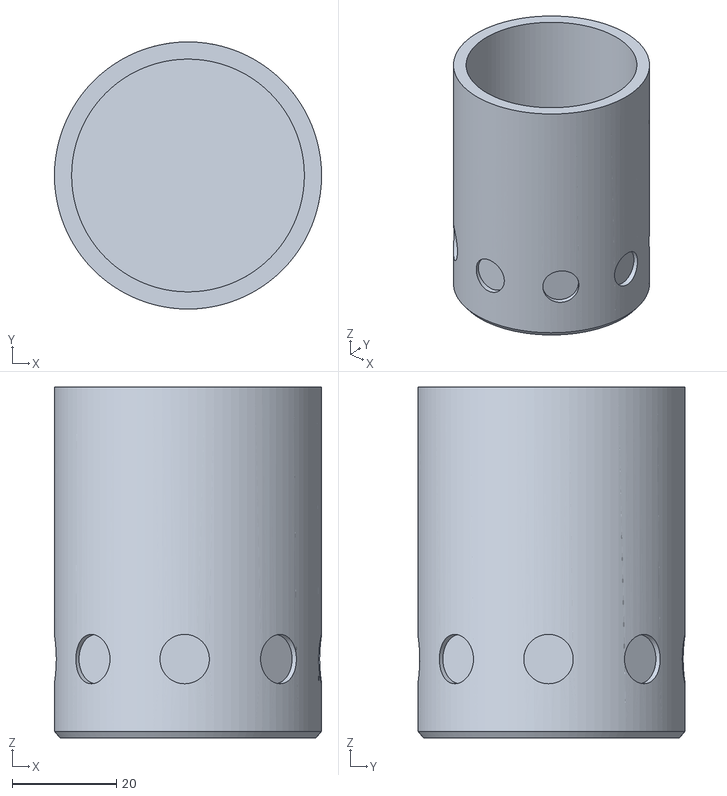
[picture p96: CAD file, 2017-09-11]
Model/83_Percent_Pack/cyclotron_1_closed.stl
51.4 x 51.4 x 67.5
