CountDeMonet/ArduinoProtonPack/Model/83_Percent_Pack/dale.stl

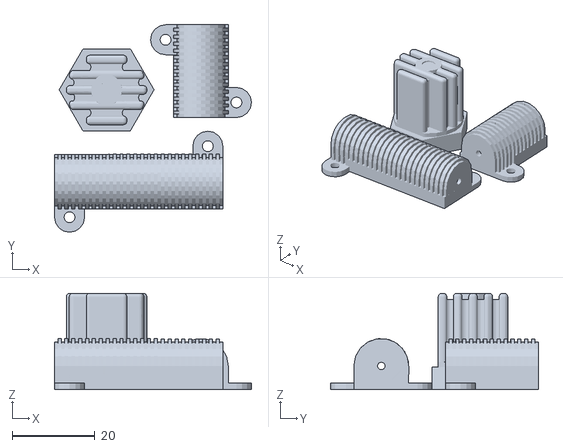
[picture p97: CAD file, 2017-09-11]
Model/83_Percent_Pack/dale.stl
47.5 x 50.1 x 23.2
