CountDeMonet/ArduinoProtonPack/Model/83_Percent_Pack/booster_4.stl

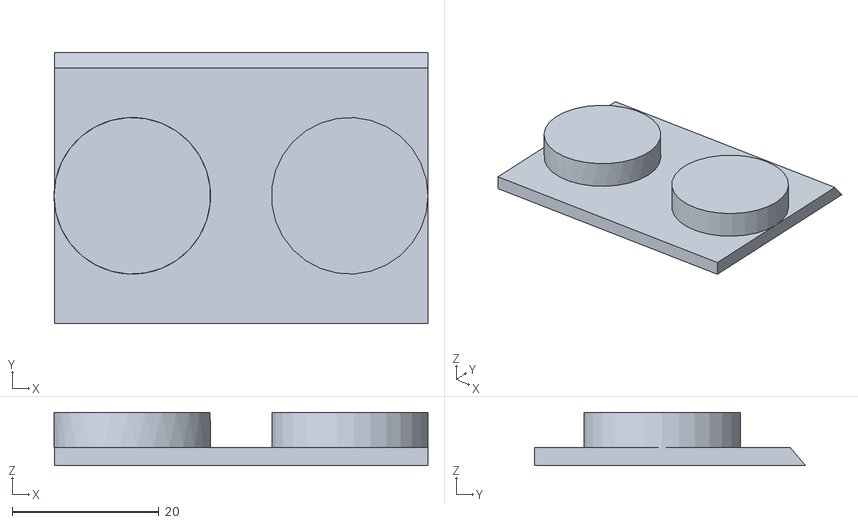
[picture p98: CAD file, 2017-09-11]
Model/83_Percent_Pack/booster_4.stl
51.0 x 37.0 x 7.27
