CountDeMonet/ArduinoProtonPack/Model/83_Percent_Pack/powercell_2.stl

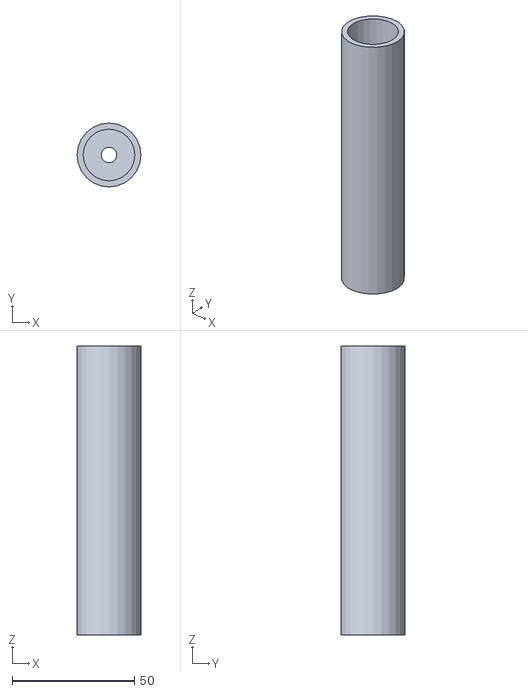
[picture p99: CAD file, 2017-09-11]
Model/83_Percent_Pack/powercell_2.stl
26.1 x 26.1 x 118.3
