CountDeMonet/ArduinoProtonPack/Model/83_Percent_Pack/tab.stl

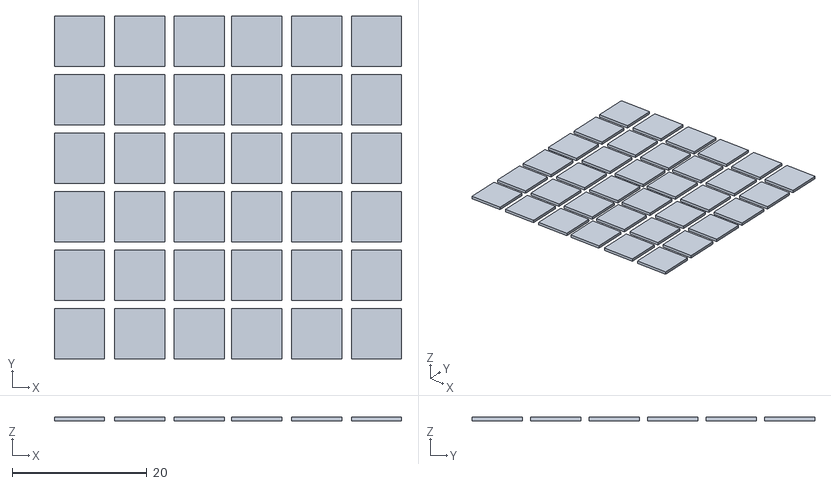
[picture p100: CAD file, 2017-09-11]
Model/83_Percent_Pack/tab.stl
51.5 x 50.8 x 0.581
