CountDeMonet/ArduinoProtonPack/Model/83_Percent_Pack/bumper_3.stl

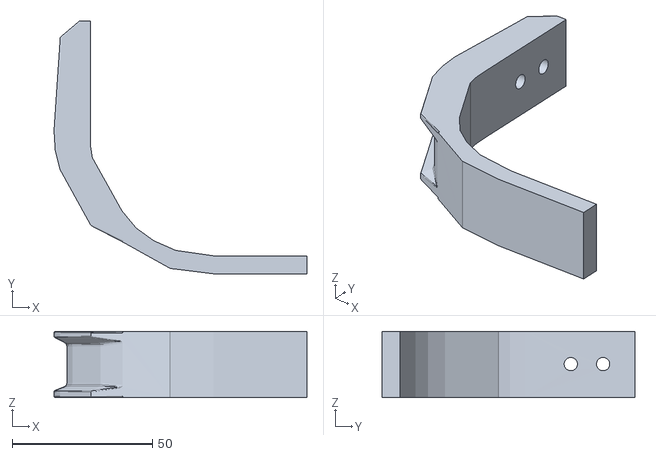
[picture p101: CAD file, 2017-09-11]
Model/83_Percent_Pack/bumper_3.stl
90.3 x 90.2 x 23.6
