CountDeMonet/ArduinoProtonPack/eagle_proton_pack_neopixel_driver_wiring_example.png

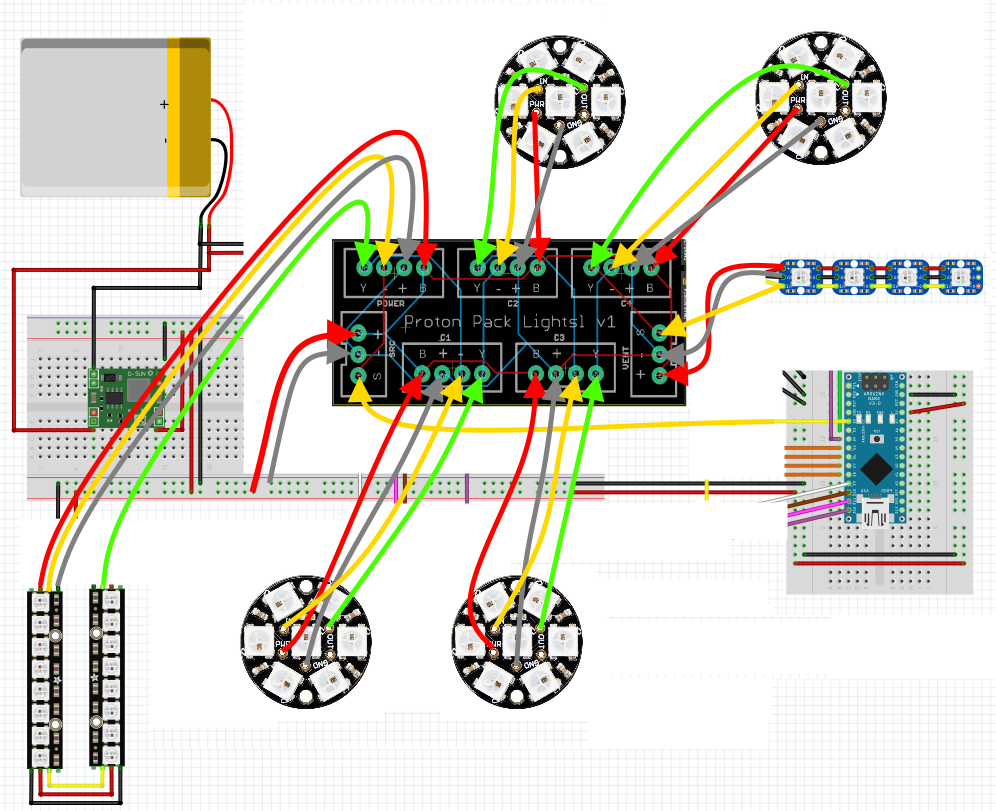
eagle_proton_pack_neopixel_driver_wiring_example.png
